Yakir-Shlez/AutoChess/Imgaes/Board/Board Inside 1.jpg

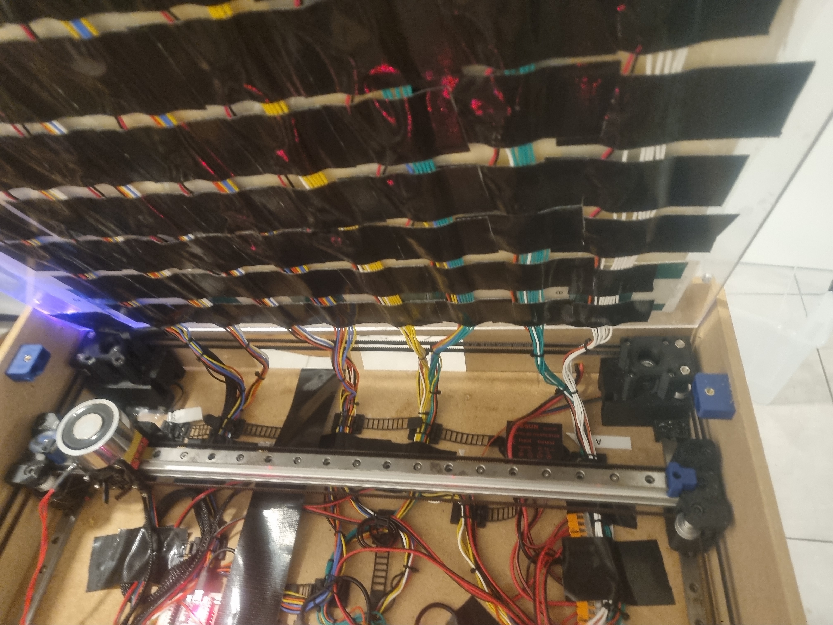
Imgaes/Board/Board Inside 1.jpg
