Yakir-Shlez/AutoChess/Imgaes/Board/Board Inside 2.jpg

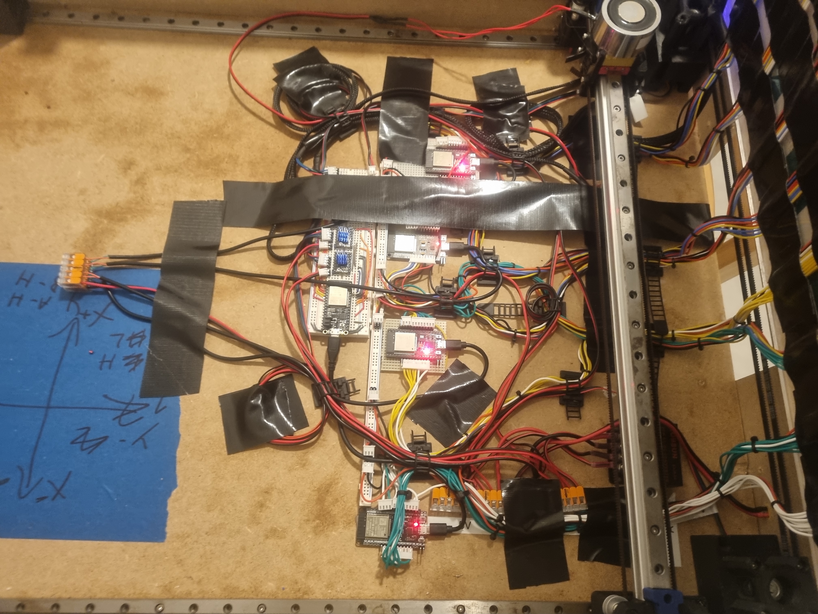
Imgaes/Board/Board Inside 2.jpg
