Yakir-Shlez/AutoChess/Imgaes/Board/Board Outside 1.jpg

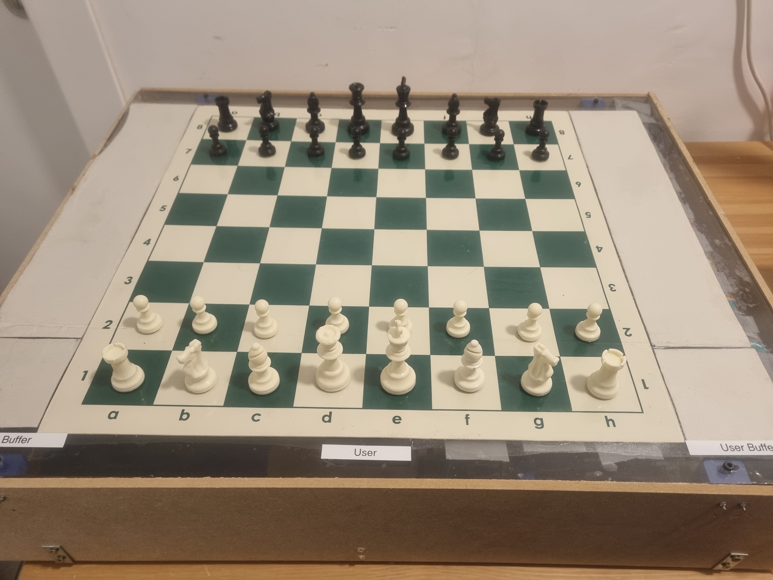
Imgaes/Board/Board Outside 1.jpg
