Yakir-Shlez/AutoChess/Imgaes/Board/Board Outside 2.jpg

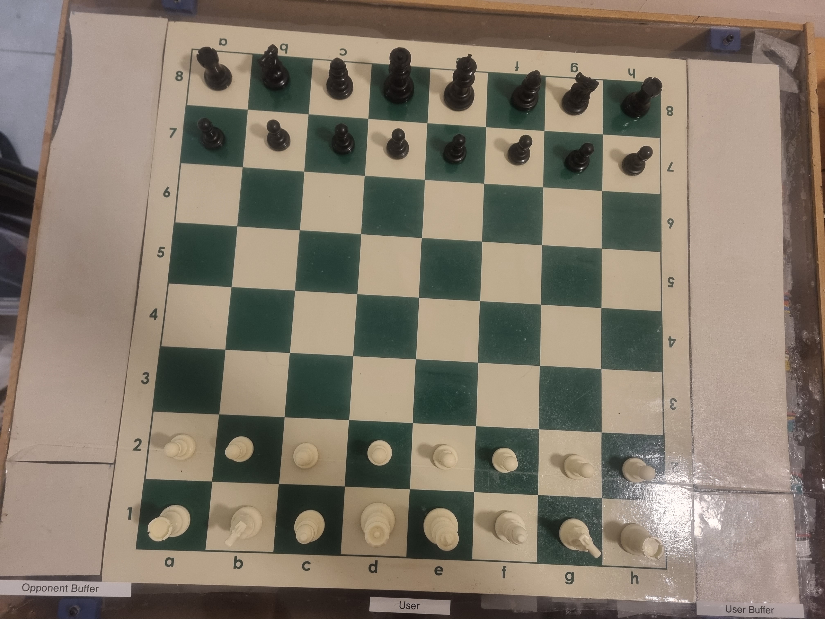
Imgaes/Board/Board Outside 2.jpg
