Yakir-Shlez/AutoChess/Imgaes/Client/Game Screen.PNG

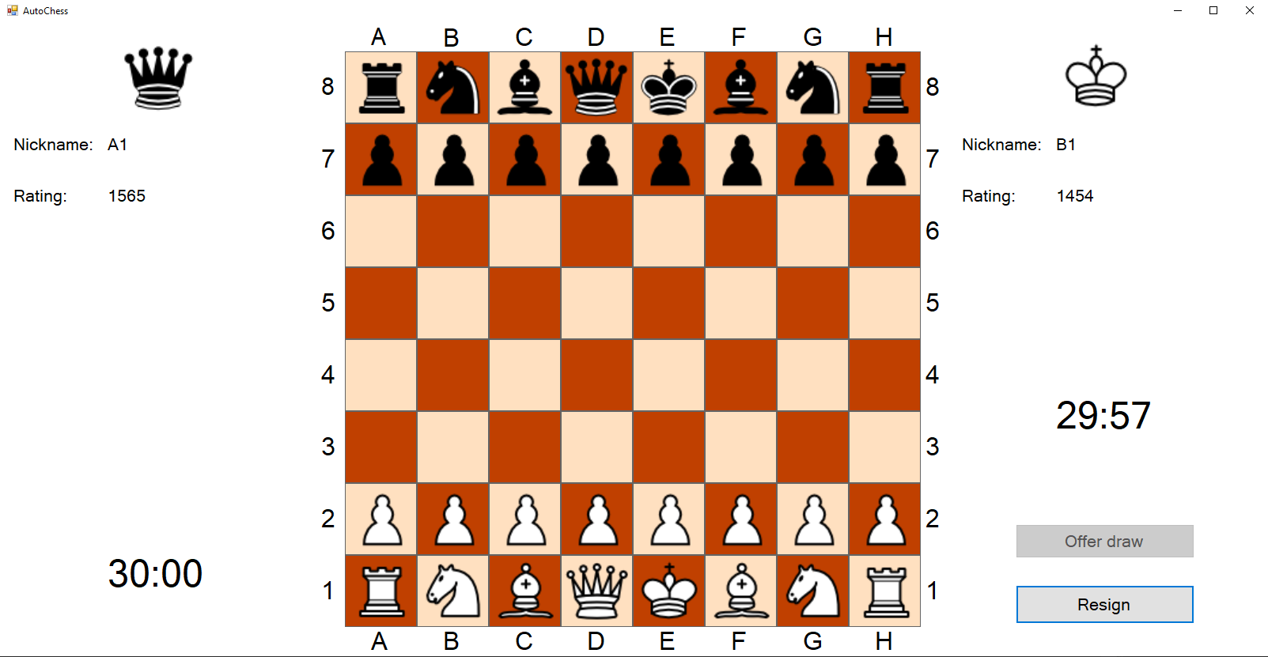
Imgaes/Client/Game Screen.PNG
