Yakir-Shlez/AutoChess/Imgaes/Client/Log In Screen.PNG

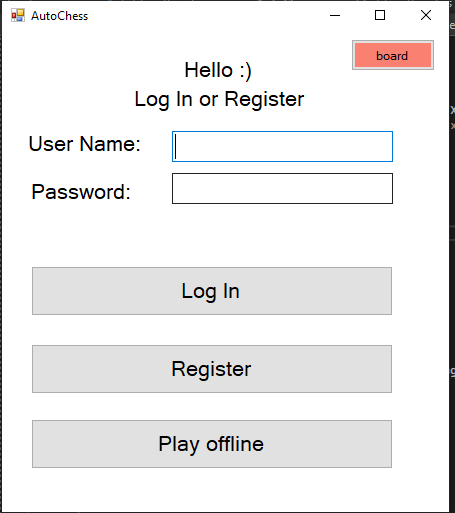
Imgaes/Client/Log In Screen.PNG
