Yakir-Shlez/AutoChess/Imgaes/Client/Main Menu Screen.PNG

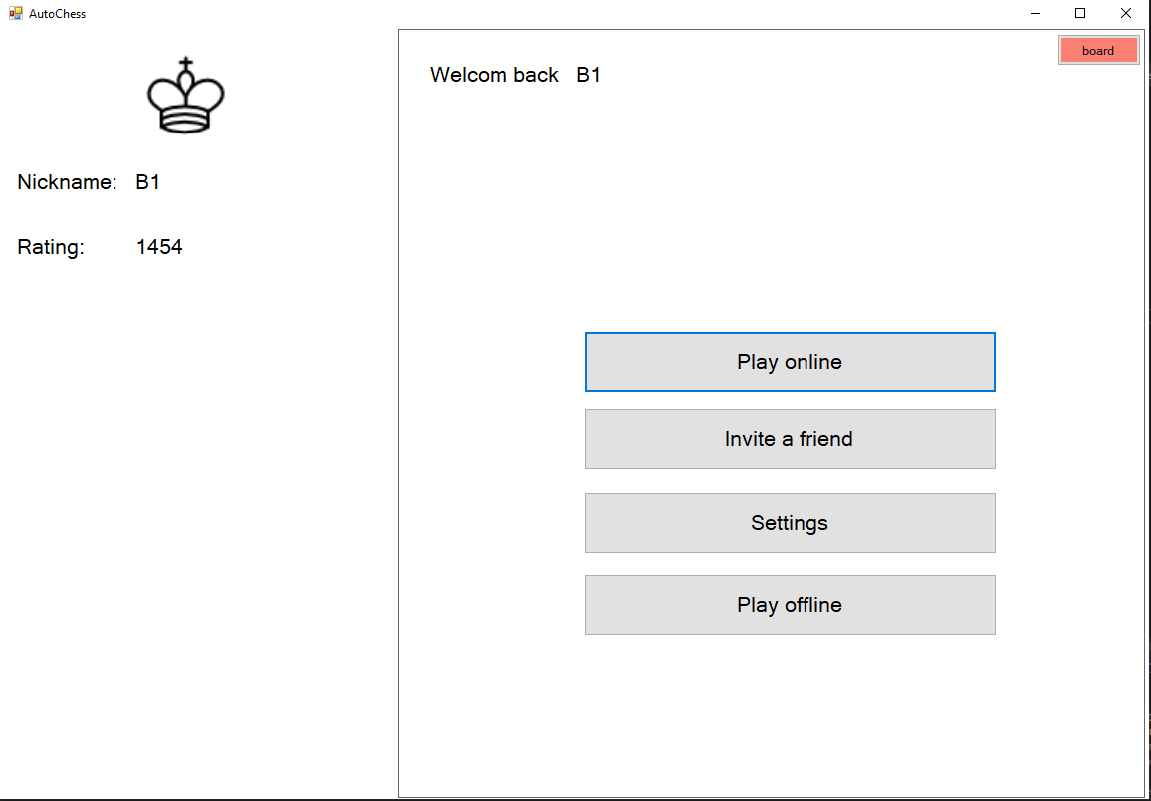
Imgaes/Client/Main Menu Screen.PNG
