Yakir-Shlez/AutoChess/Imgaes/Server/Server Off.jpg

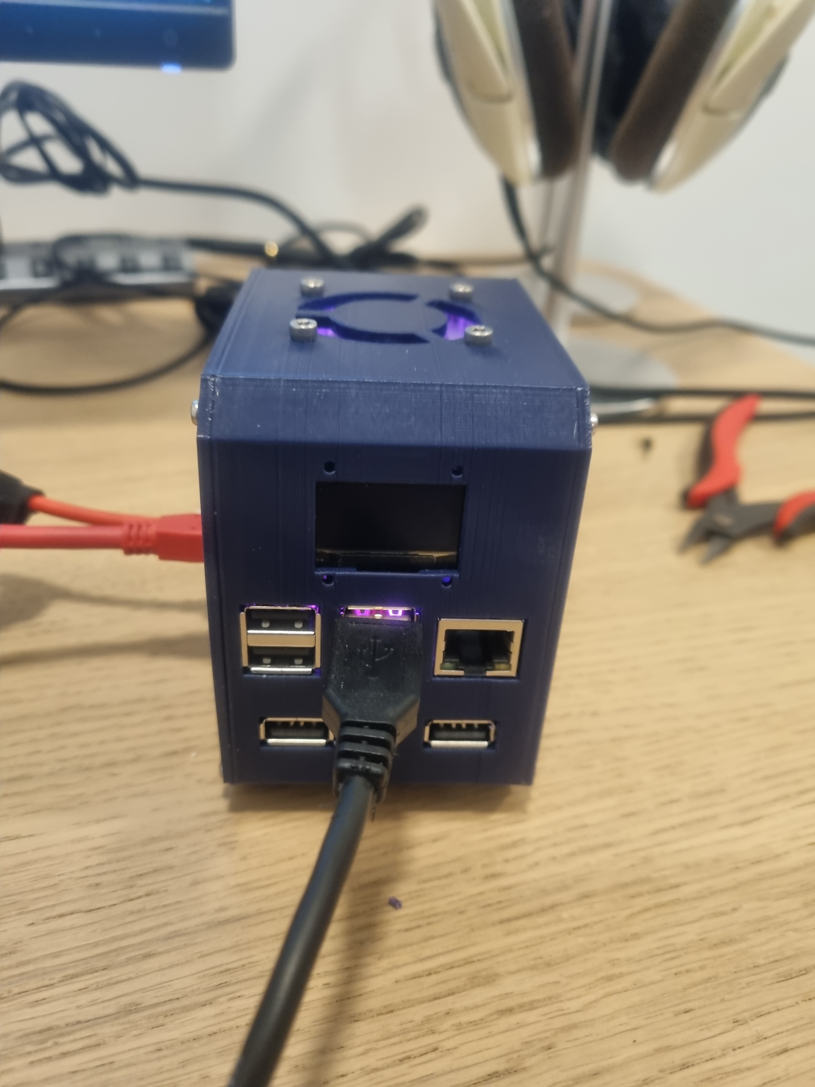
Imgaes/Server/Server Off.jpg
