Yakir-Shlez/AutoChess/Imgaes/Server/Server On.jpg

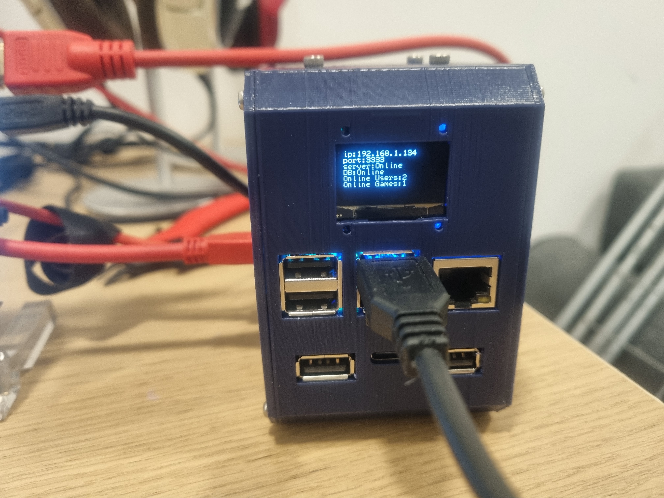
Imgaes/Server/Server On.jpg
