Yakir-Shlez/AutoChess/Imgaes/Server/Server Open.jpg

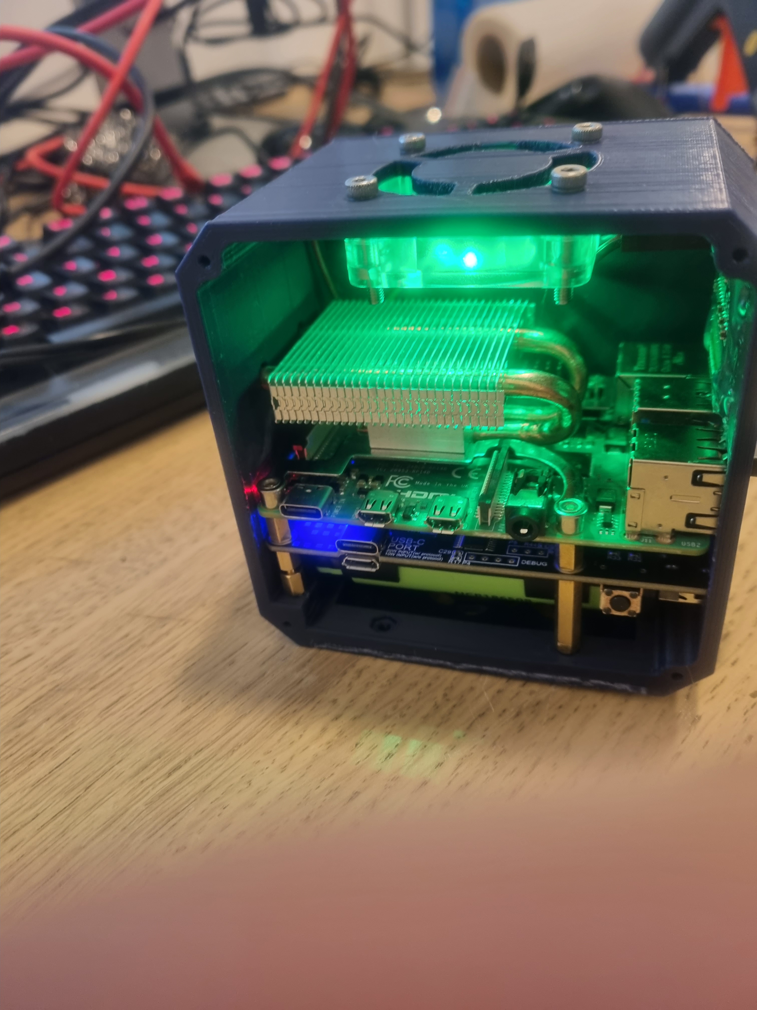
Imgaes/Server/Server Open.jpg
