Yakir-Shlez/AutoChess/Imgaes/Server/Server Screen.jpg

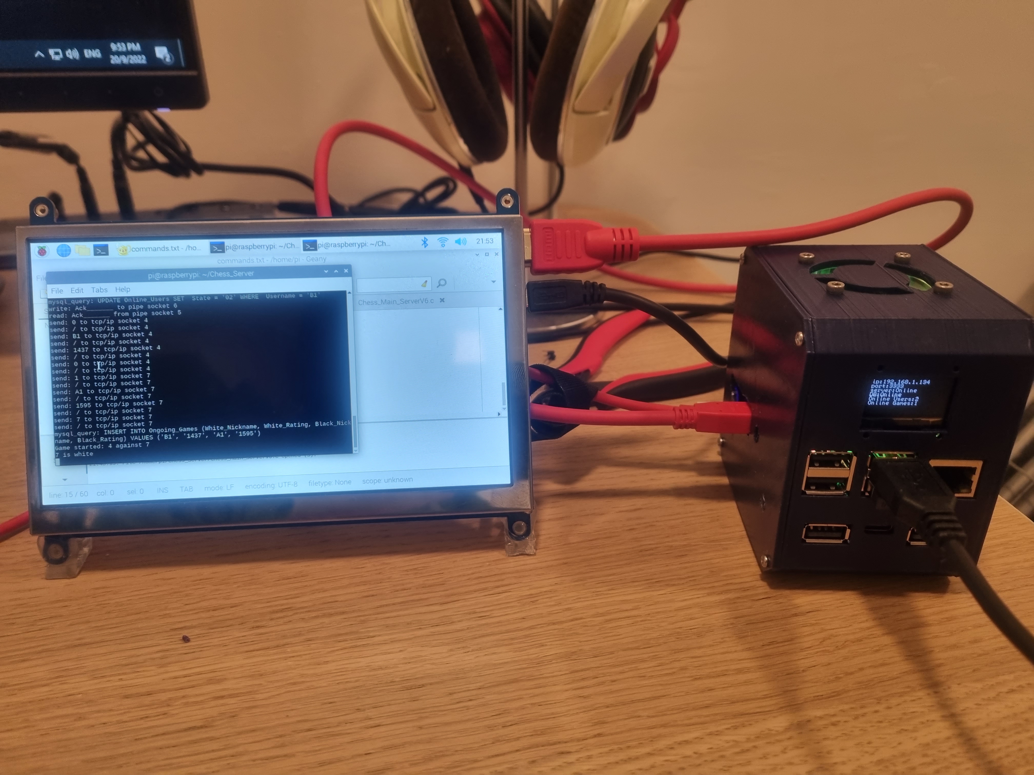
Imgaes/Server/Server Screen.jpg
