Yakir-Shlez/AutoChess/Imgaes/WIP/20210708_012601.jpg

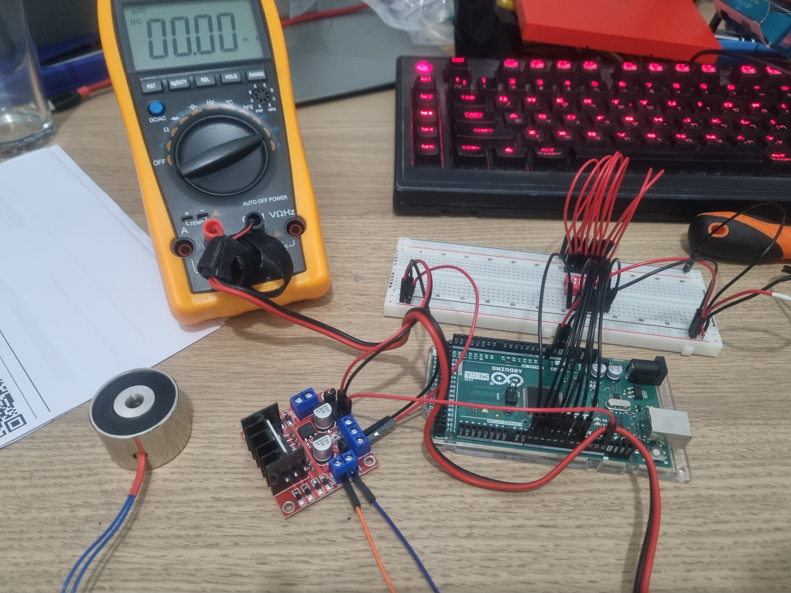
Imgaes/WIP/20210708_012601.jpg
