Yakir-Shlez/AutoChess/Imgaes/WIP/20210708_012740.jpg

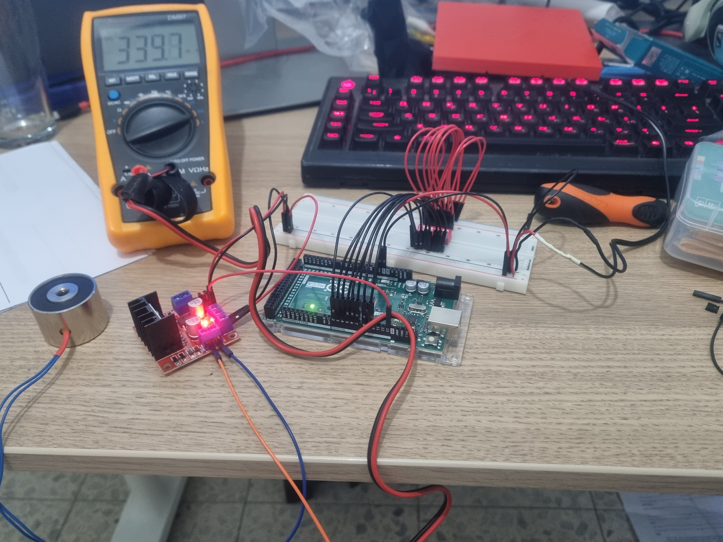
Imgaes/WIP/20210708_012740.jpg
