Yakir-Shlez/AutoChess/Imgaes/WIP/20210708_191133.jpg

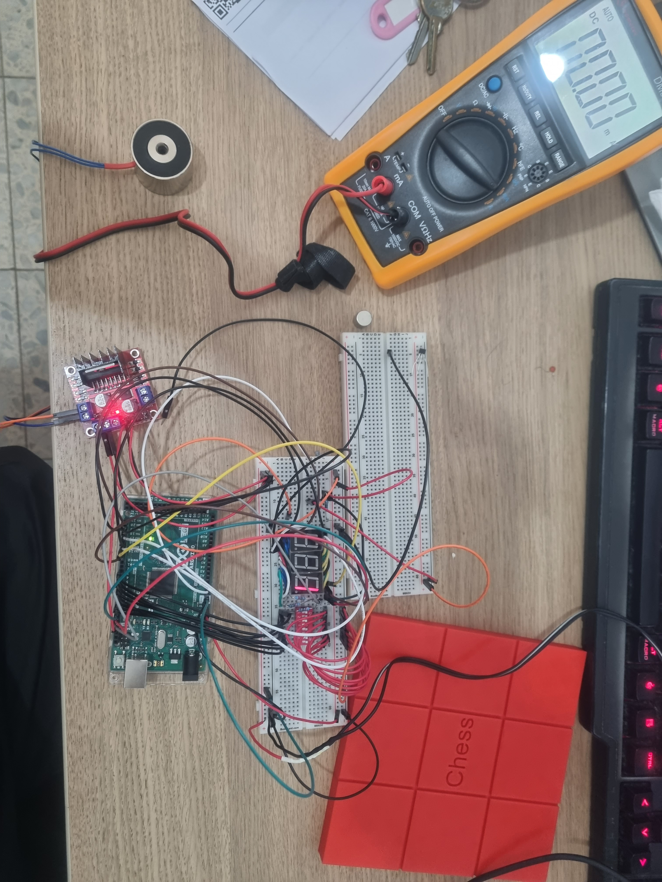
Imgaes/WIP/20210708_191133.jpg
