Yakir-Shlez/AutoChess/Imgaes/WIP/20210709_002144.jpg

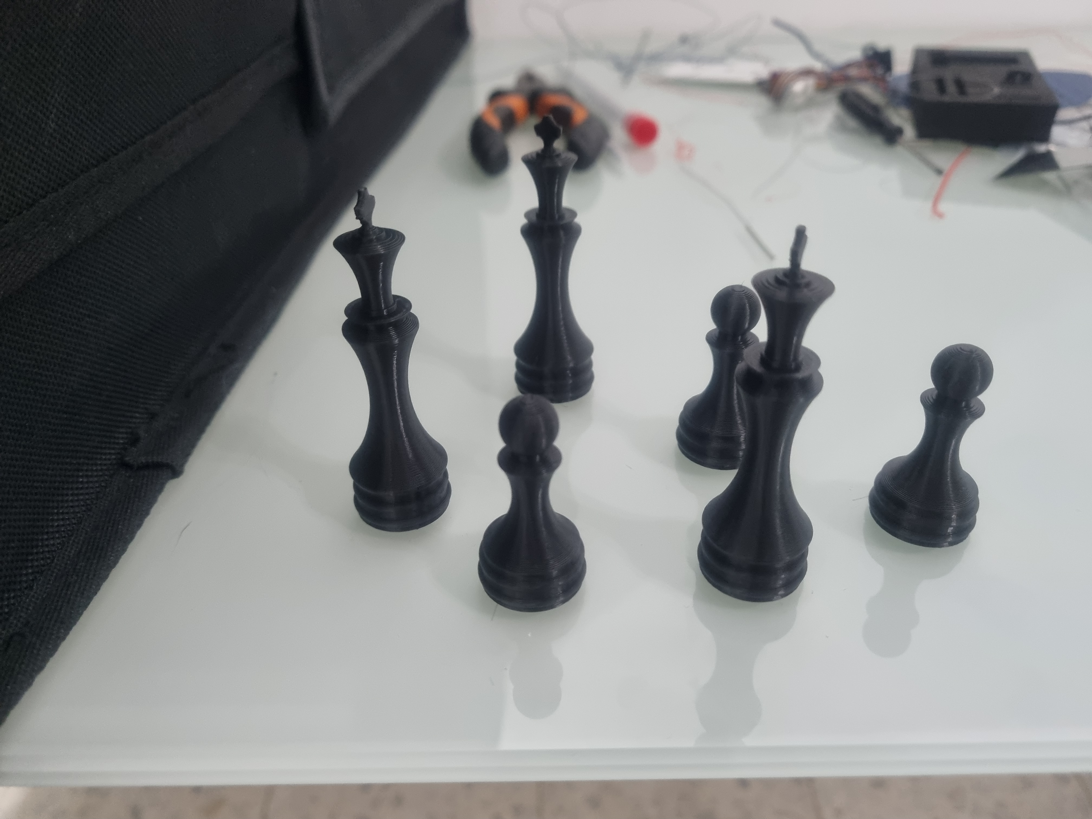
Imgaes/WIP/20210709_002144.jpg
