Yakir-Shlez/AutoChess/Imgaes/WIP/20210709_173027.jpg

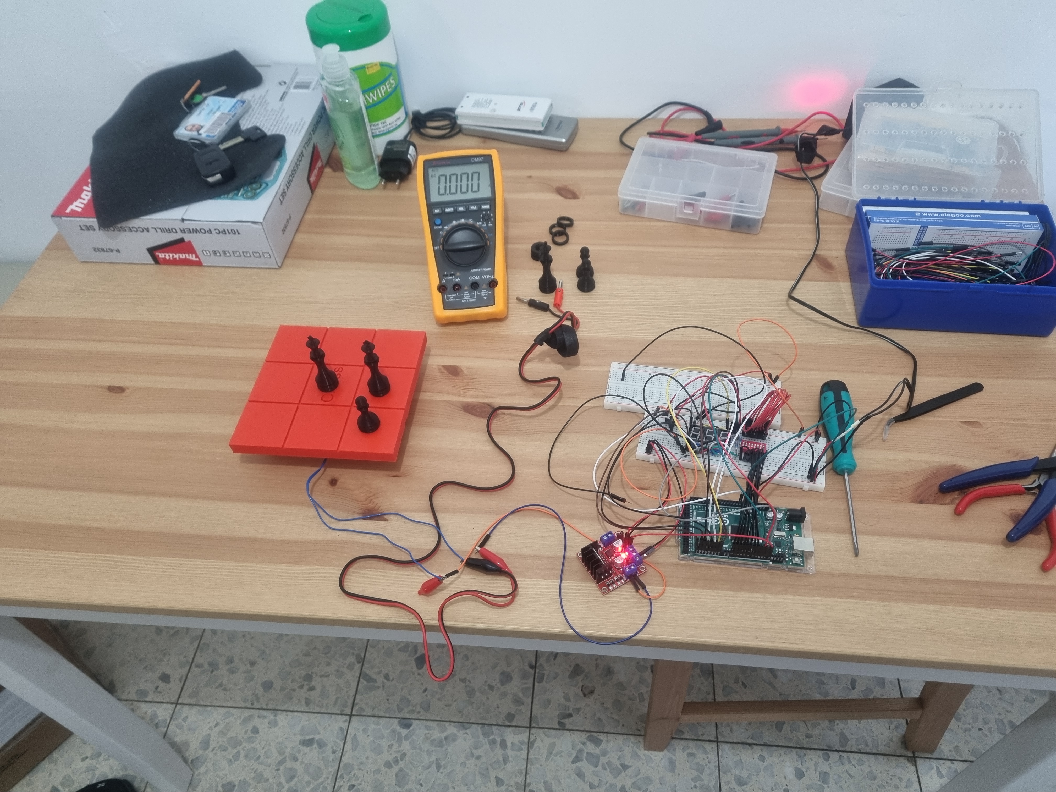
Imgaes/WIP/20210709_173027.jpg
