Yakir-Shlez/AutoChess/Imgaes/WIP/20210715_232516.jpg

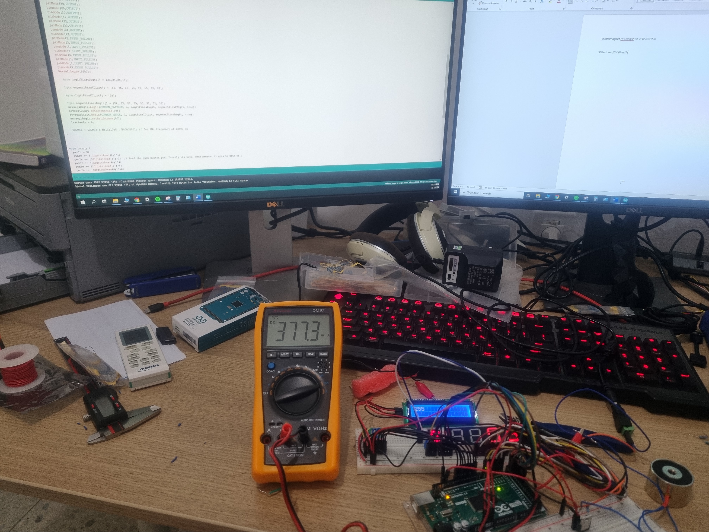
Imgaes/WIP/20210715_232516.jpg
