Yakir-Shlez/AutoChess/Imgaes/WIP/20210715_232529.jpg

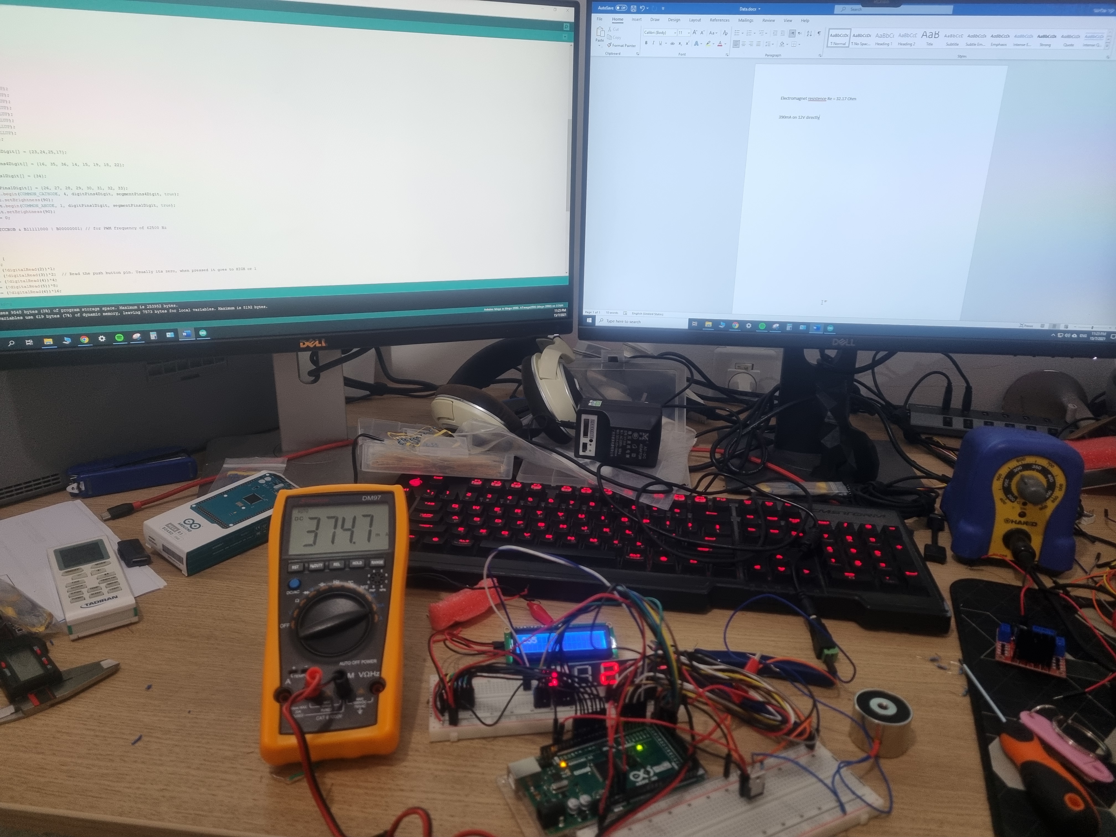
Imgaes/WIP/20210715_232529.jpg
