Yakir-Shlez/AutoChess/Imgaes/WIP/20210715_232534.jpg

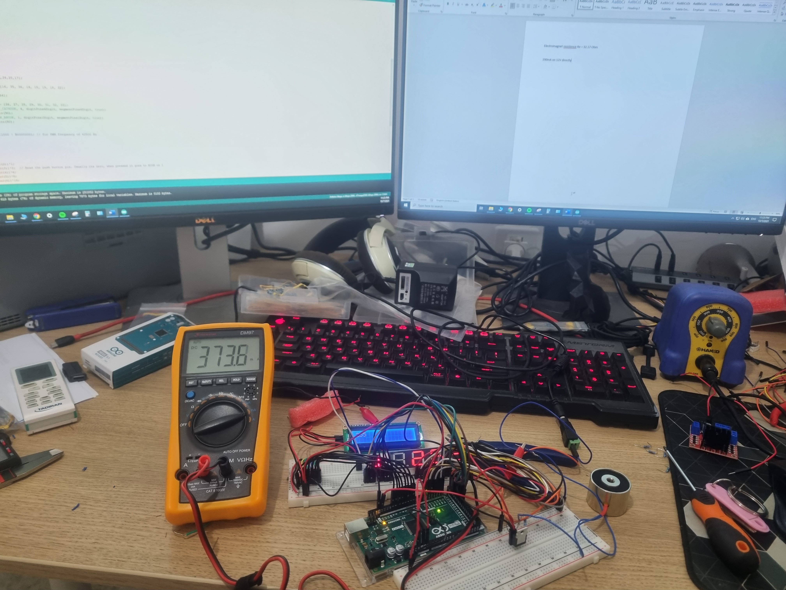
Imgaes/WIP/20210715_232534.jpg
