Yakir-Shlez/AutoChess/Imgaes/WIP/20210715_232541.jpg

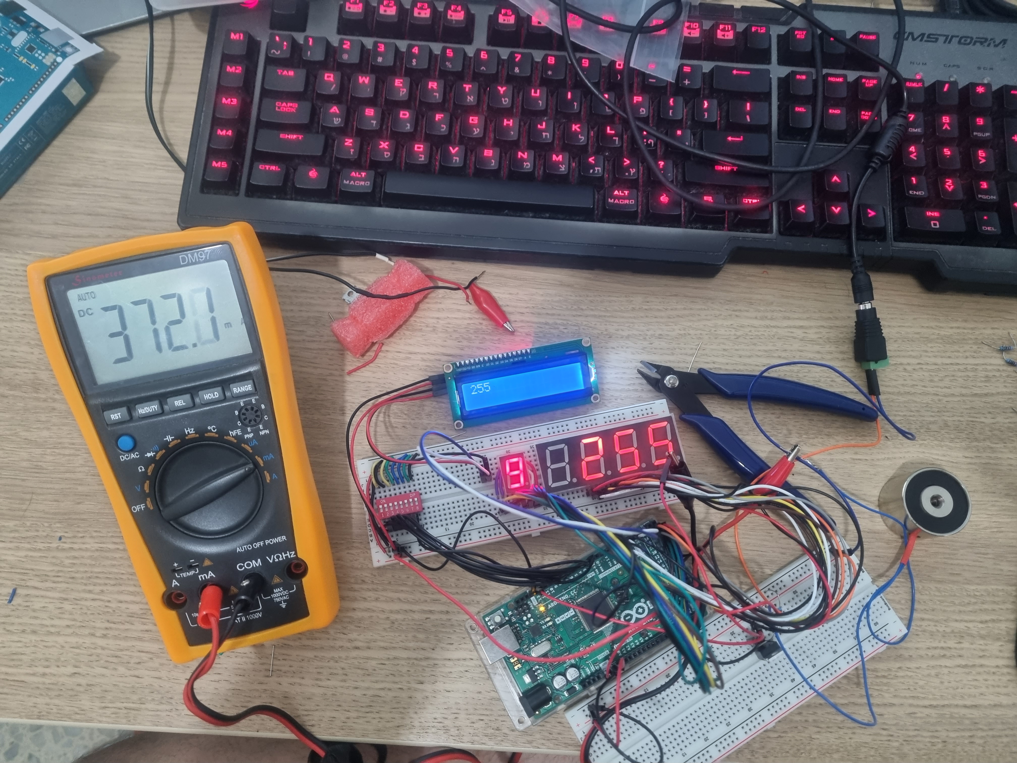
Imgaes/WIP/20210715_232541.jpg
