Yakir-Shlez/AutoChess/Imgaes/WIP/20210722_215017.jpg

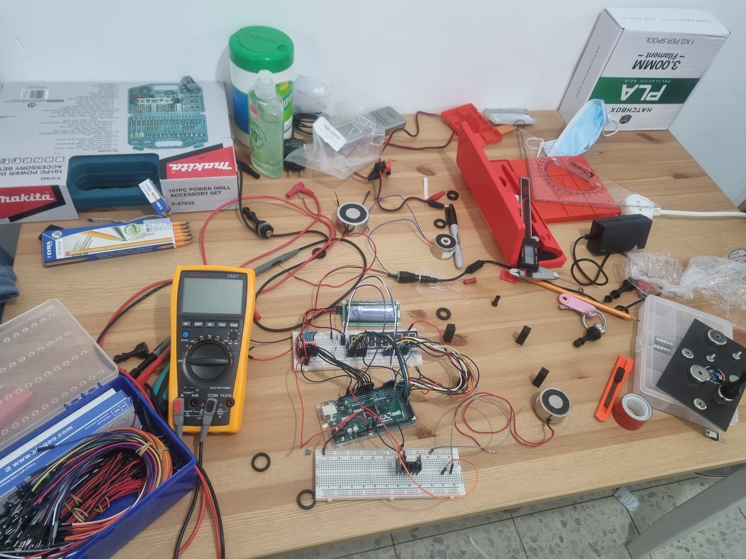
Imgaes/WIP/20210722_215017.jpg
