Yakir-Shlez/AutoChess/Imgaes/WIP/20210724_002252.jpg

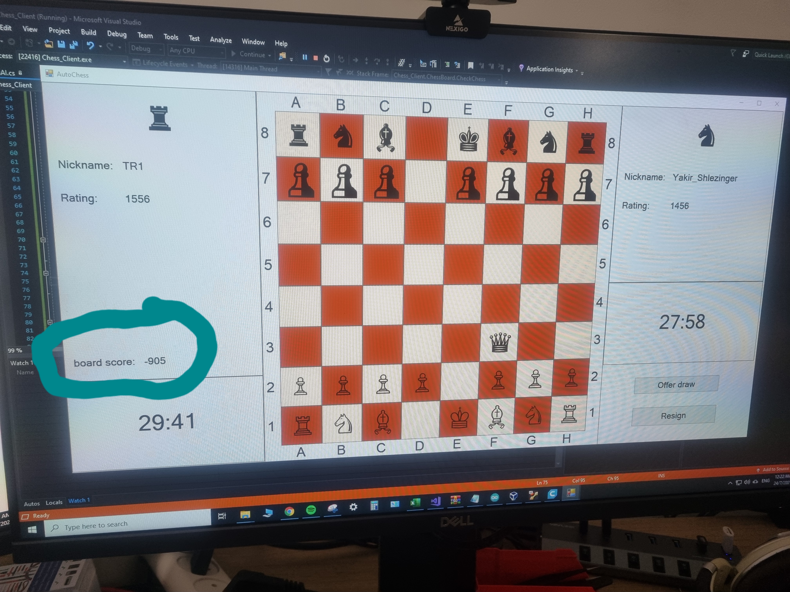
Imgaes/WIP/20210724_002252.jpg
