Yakir-Shlez/AutoChess/Imgaes/WIP/20210724_130340.jpg

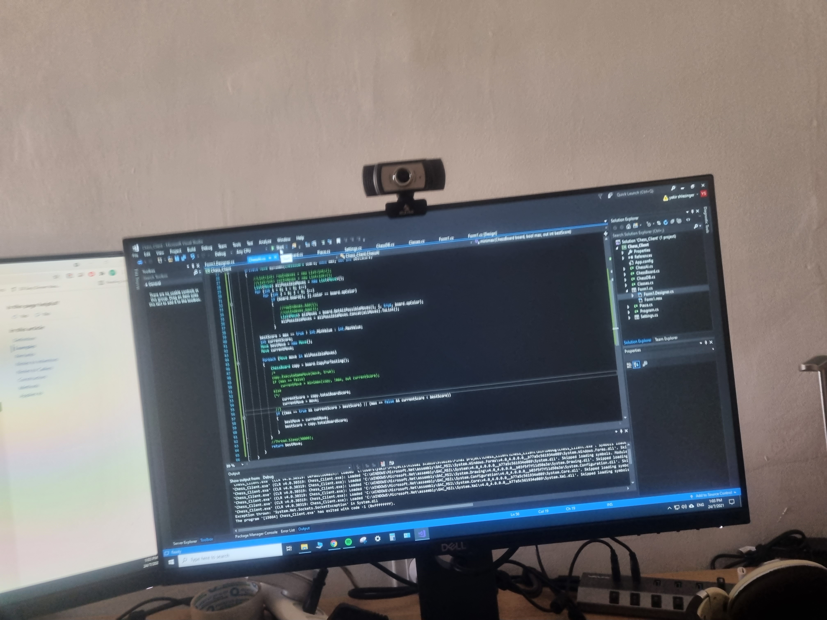
Imgaes/WIP/20210724_130340.jpg
