Yakir-Shlez/AutoChess/Imgaes/WIP/20210727_054952.jpg

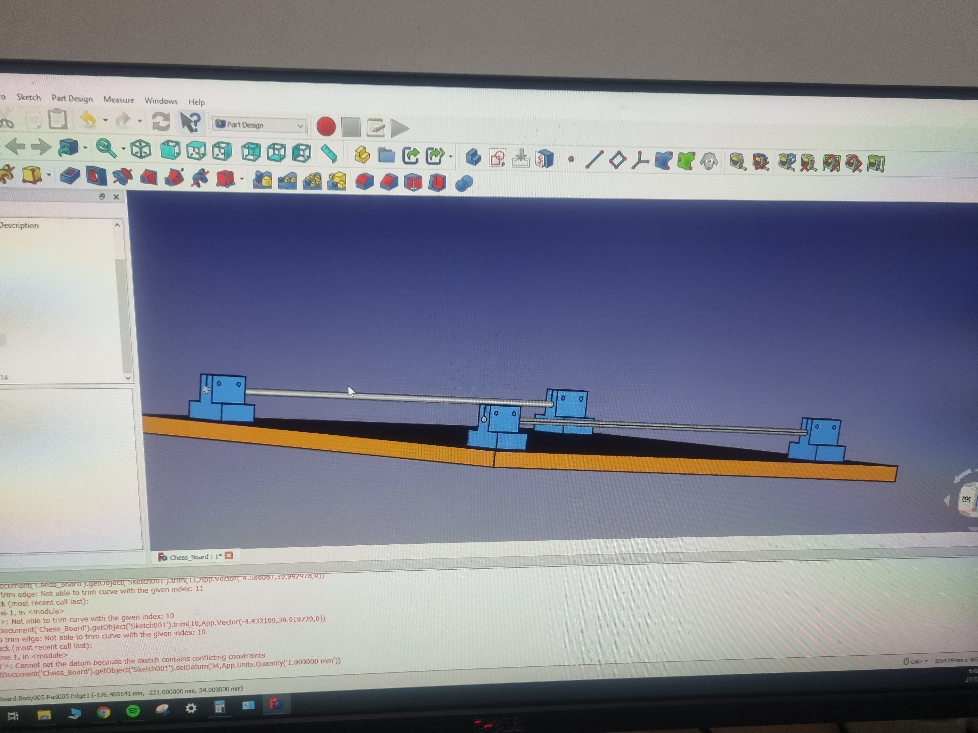
Imgaes/WIP/20210727_054952.jpg
