Yakir-Shlez/AutoChess/Imgaes/WIP/20210731_223613.jpg

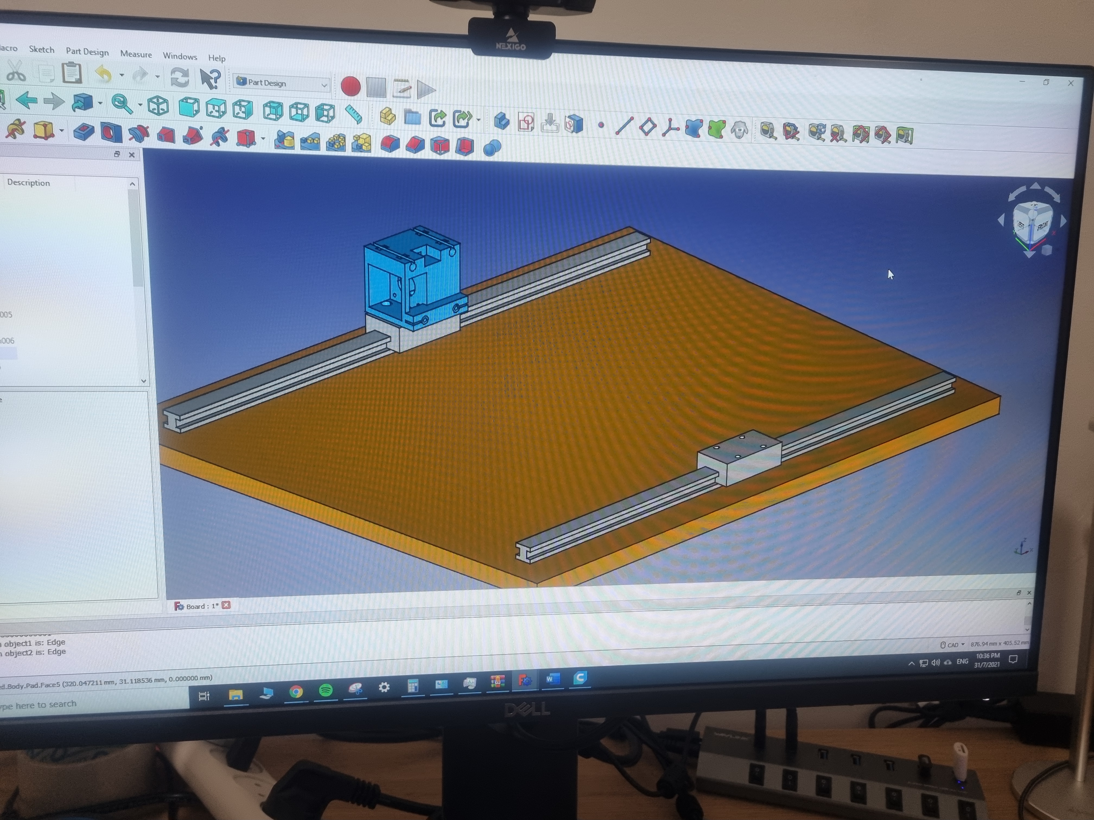
Imgaes/WIP/20210731_223613.jpg
