Yakir-Shlez/AutoChess/Imgaes/WIP/20210731_234115.jpg

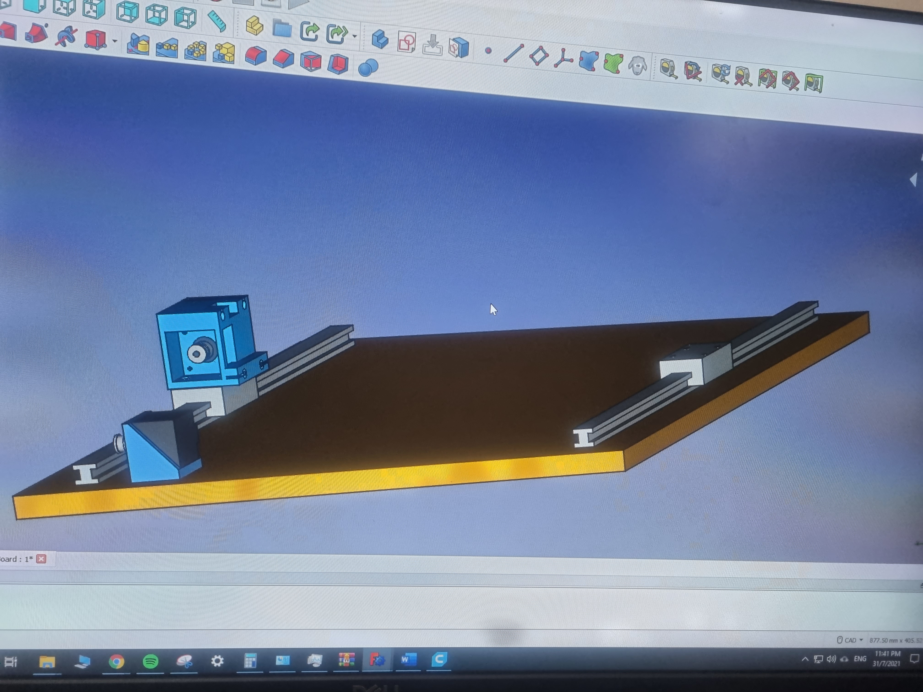
Imgaes/WIP/20210731_234115.jpg
