Yakir-Shlez/AutoChess/Imgaes/WIP/20210801_025701.jpg

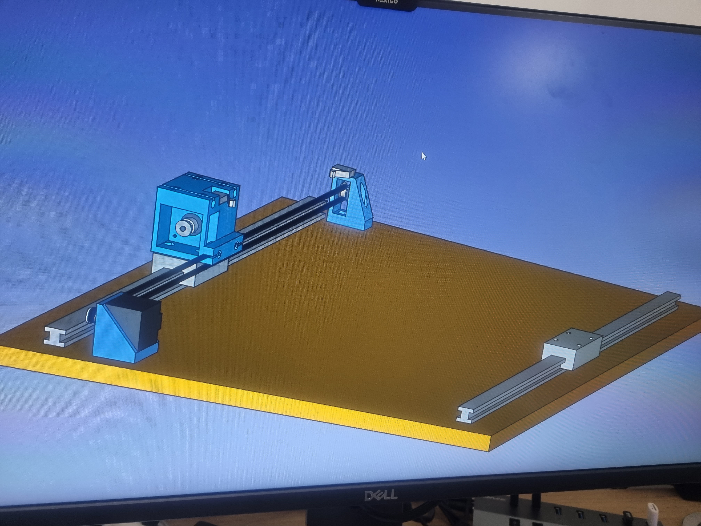
Imgaes/WIP/20210801_025701.jpg
