Yakir-Shlez/AutoChess/Imgaes/WIP/20210801_025935.jpg

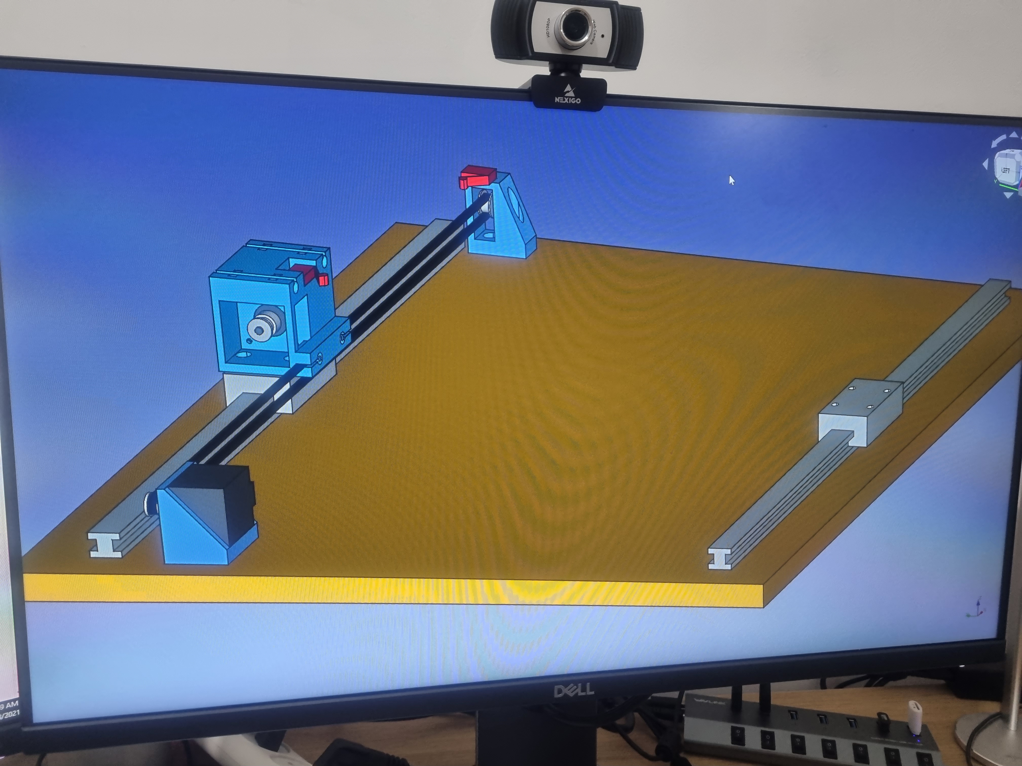
Imgaes/WIP/20210801_025935.jpg
