Yakir-Shlez/AutoChess/Imgaes/WIP/20210801_035938.jpg

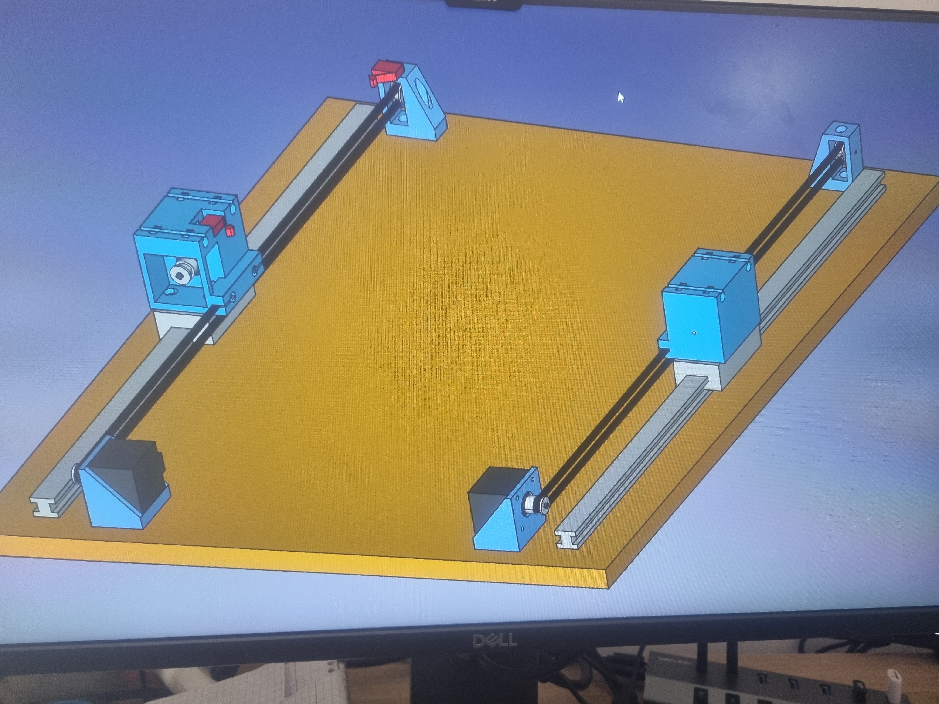
Imgaes/WIP/20210801_035938.jpg
