Yakir-Shlez/AutoChess/Imgaes/WIP/20210801_040600.jpg

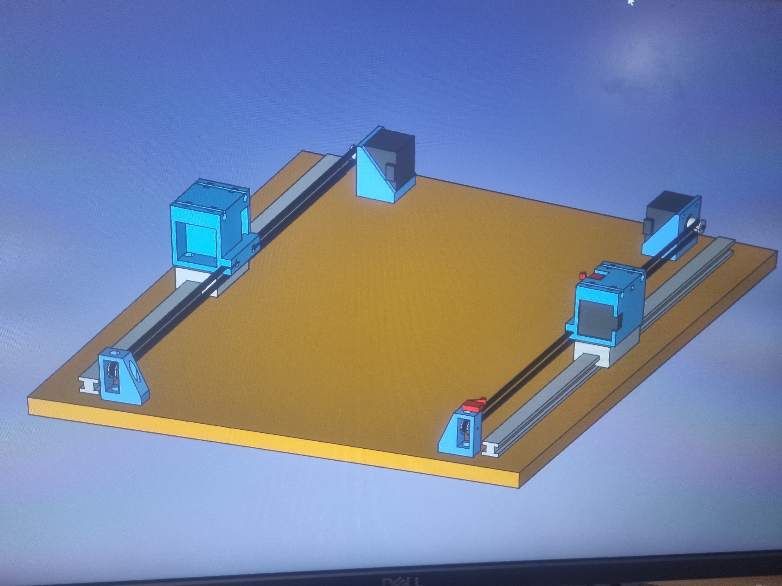
Imgaes/WIP/20210801_040600.jpg
