Yakir-Shlez/AutoChess/Imgaes/WIP/20210801_040831.jpg

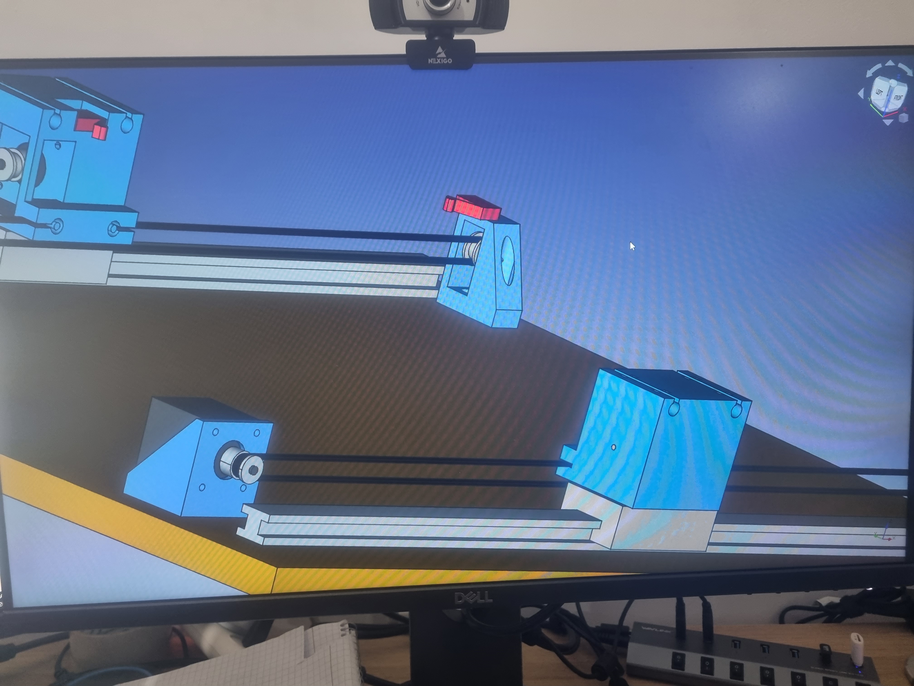
Imgaes/WIP/20210801_040831.jpg
