Yakir-Shlez/AutoChess/Imgaes/WIP/20210801_052911.jpg

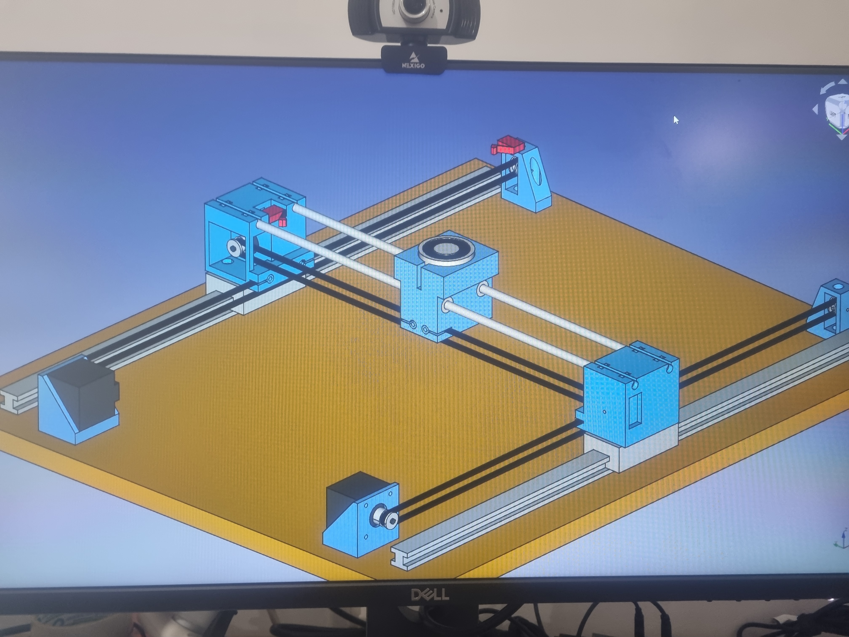
Imgaes/WIP/20210801_052911.jpg
