Yakir-Shlez/AutoChess/Imgaes/WIP/20210801_053046.jpg

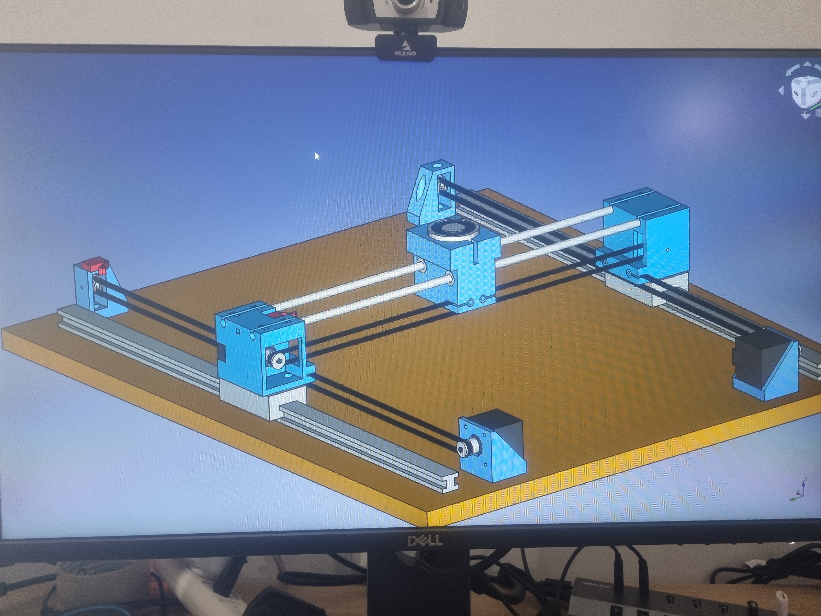
Imgaes/WIP/20210801_053046.jpg
