Yakir-Shlez/AutoChess/Imgaes/WIP/20210801_055255.jpg

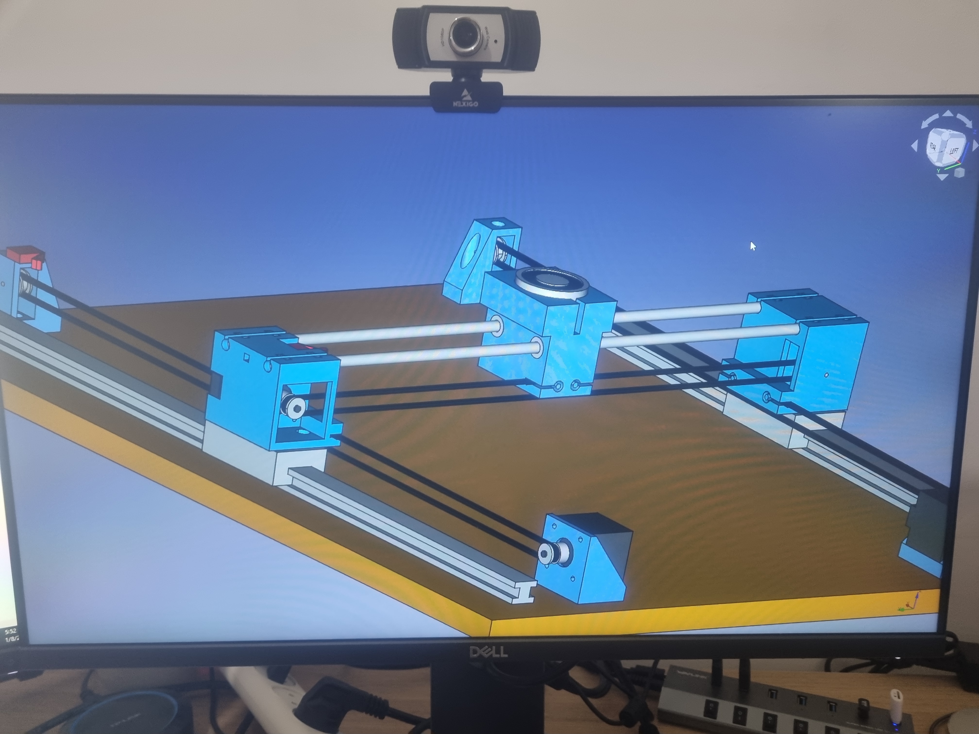
Imgaes/WIP/20210801_055255.jpg
