Yakir-Shlez/AutoChess/Imgaes/WIP/20210801_055333.jpg

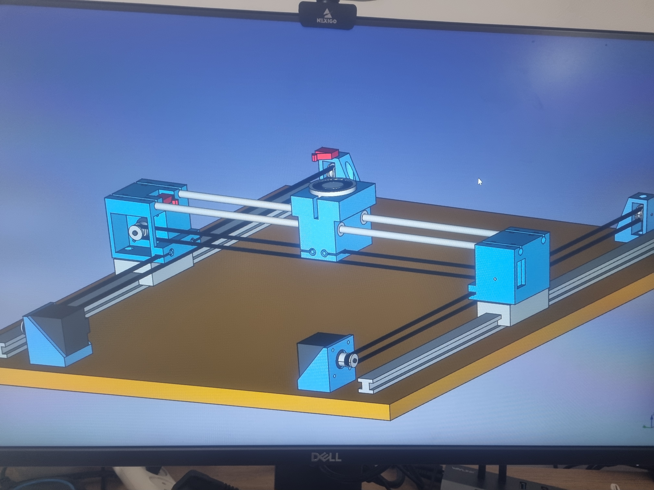
Imgaes/WIP/20210801_055333.jpg
