Yakir-Shlez/AutoChess/Imgaes/WIP/20210816_194603.jpg

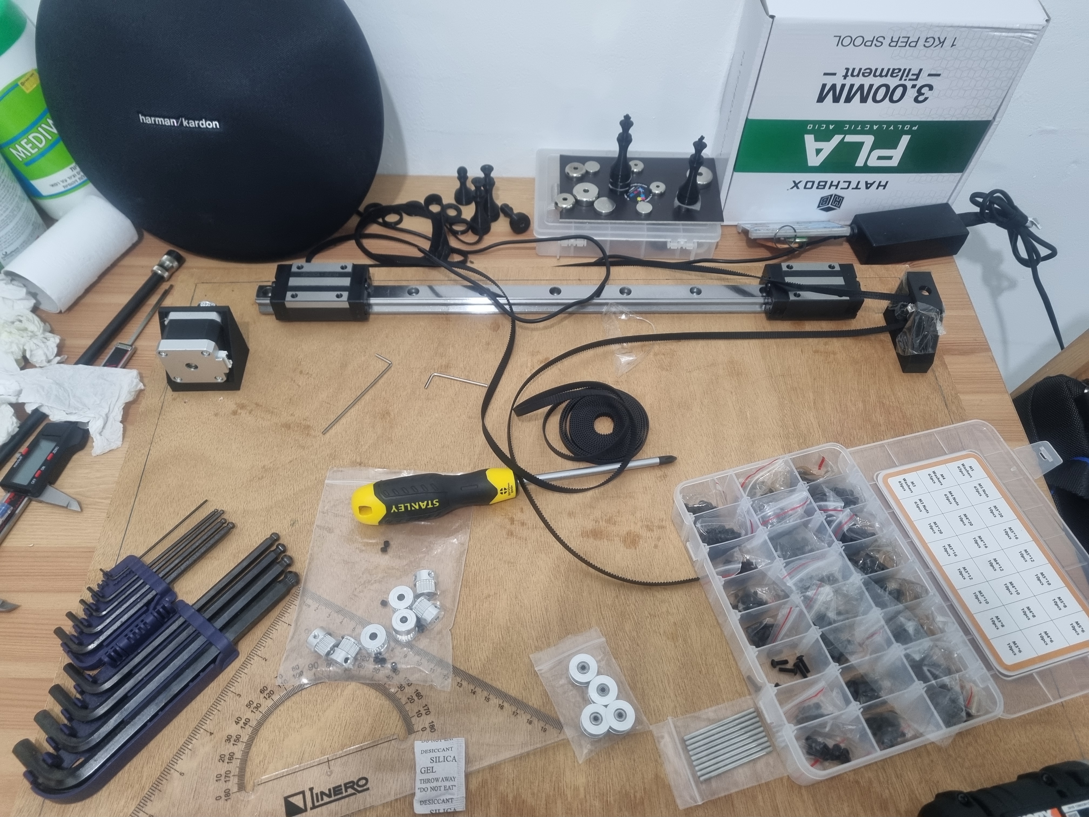
Imgaes/WIP/20210816_194603.jpg
