Yakir-Shlez/AutoChess/Imgaes/WIP/20210816_194617.jpg

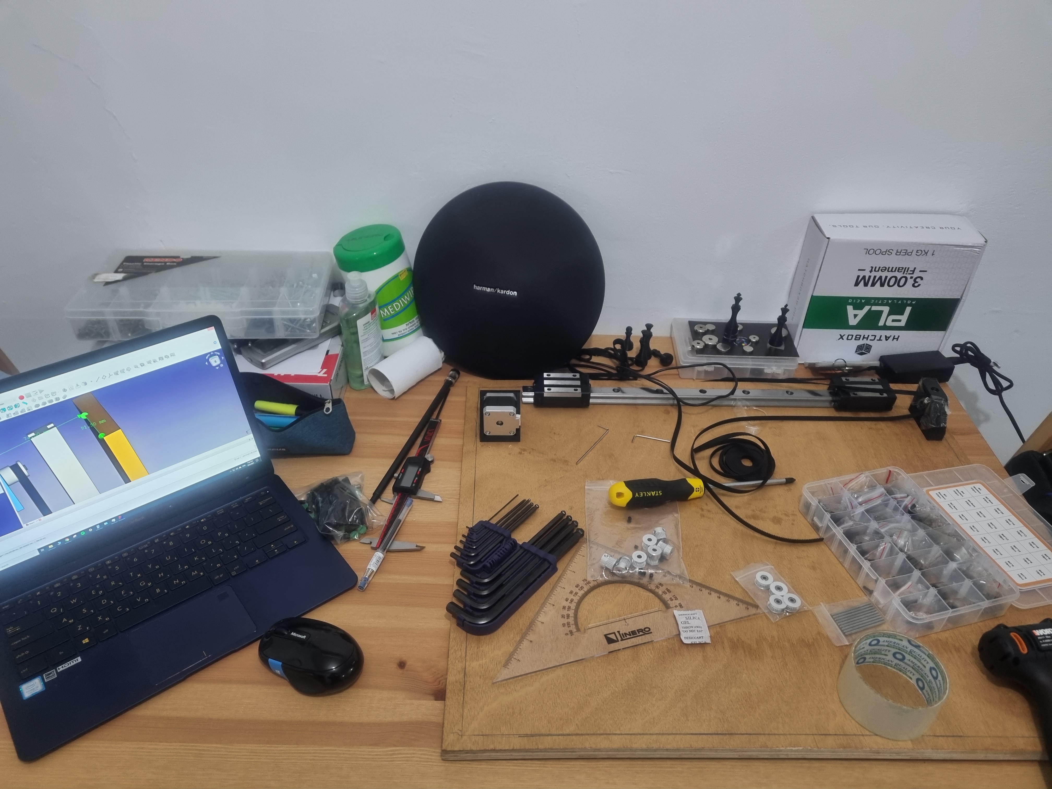
Imgaes/WIP/20210816_194617.jpg
