Yakir-Shlez/AutoChess/Imgaes/WIP/20211106_215429.jpg

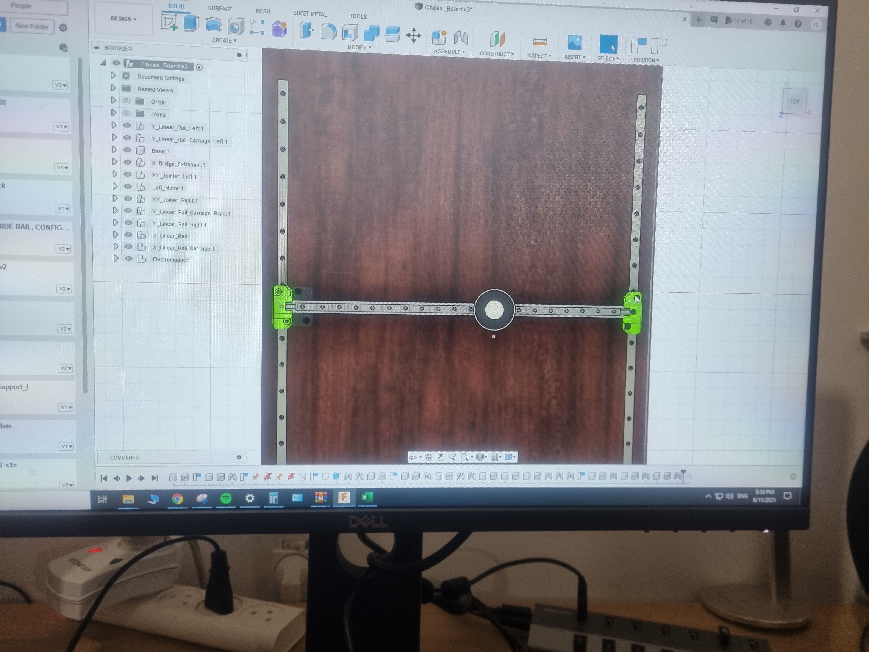
Imgaes/WIP/20211106_215429.jpg
