Yakir-Shlez/AutoChess/Imgaes/WIP/20211125_202150.jpg

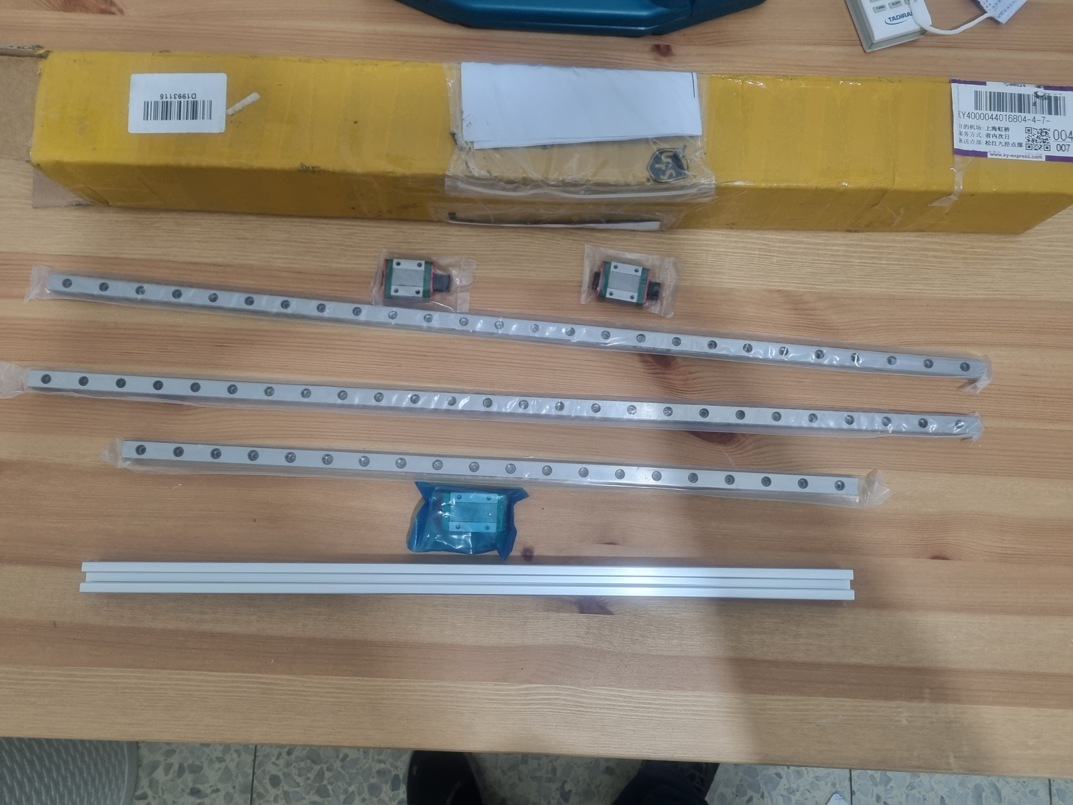
Imgaes/WIP/20211125_202150.jpg
