Yakir-Shlez/AutoChess/Imgaes/WIP/20220408_162342.jpg

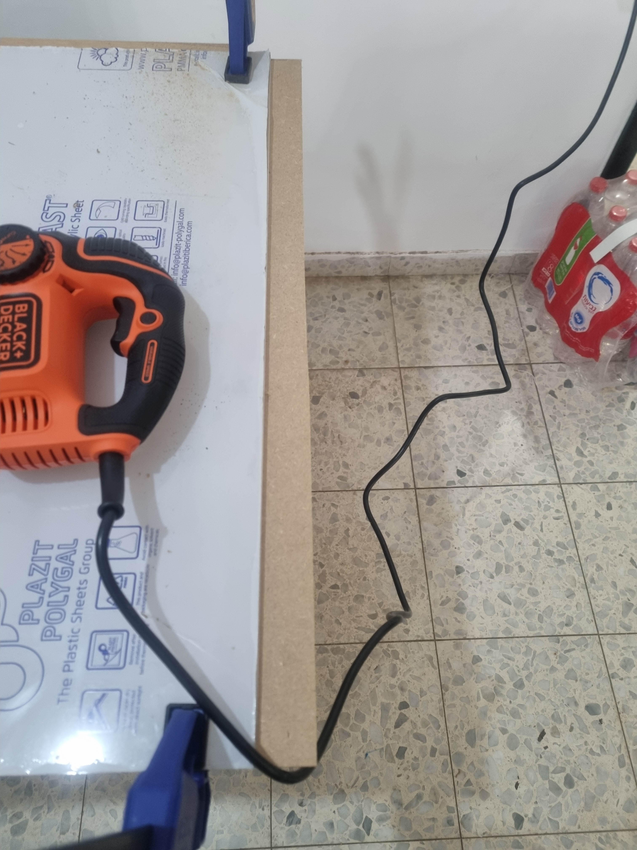
Imgaes/WIP/20220408_162342.jpg
