Yakir-Shlez/AutoChess/Imgaes/WIP/20220408_162356.jpg

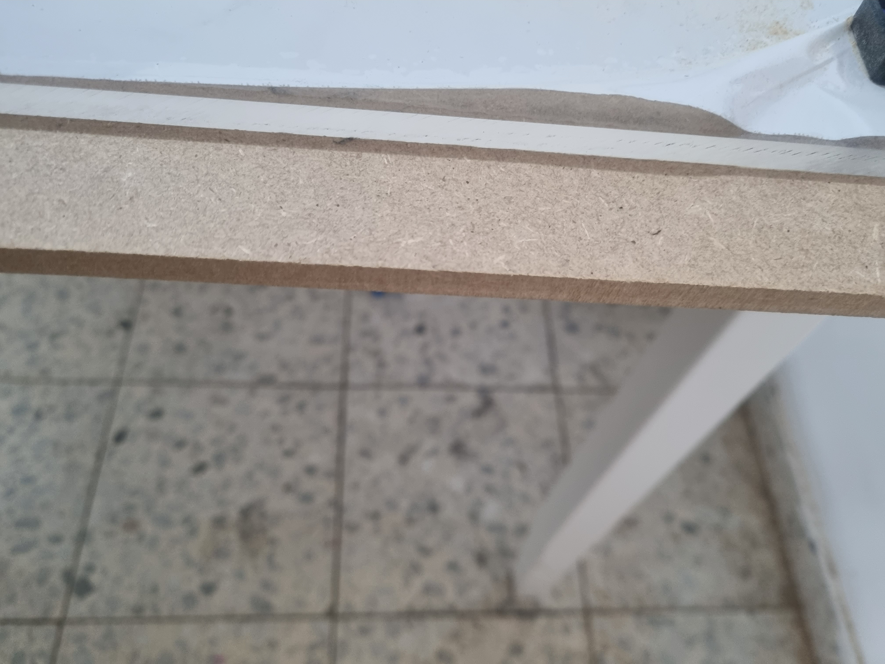
Imgaes/WIP/20220408_162356.jpg
