Yakir-Shlez/AutoChess/Imgaes/WIP/20220408_162821.jpg

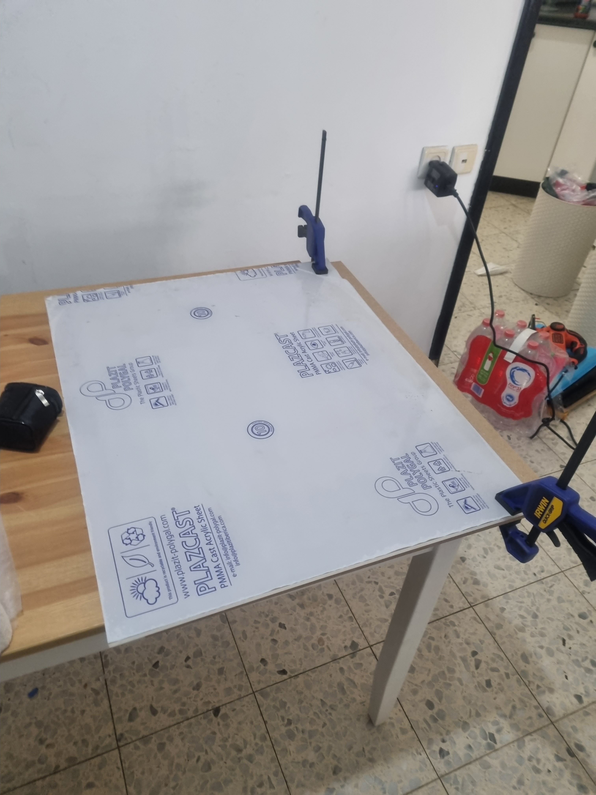
Imgaes/WIP/20220408_162821.jpg
