Yakir-Shlez/AutoChess/Imgaes/WIP/20220408_163001.jpg

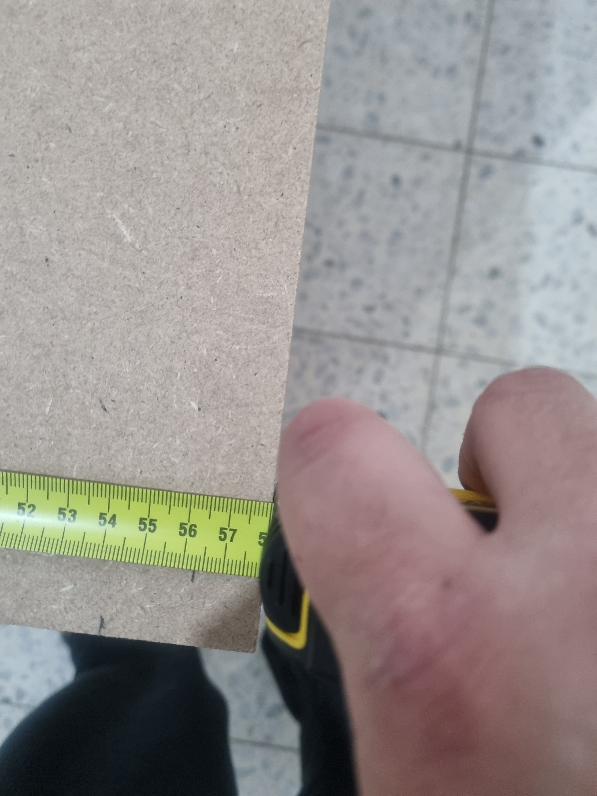
Imgaes/WIP/20220408_163001.jpg
