Yakir-Shlez/AutoChess/Imgaes/WIP/20220408_163010.jpg

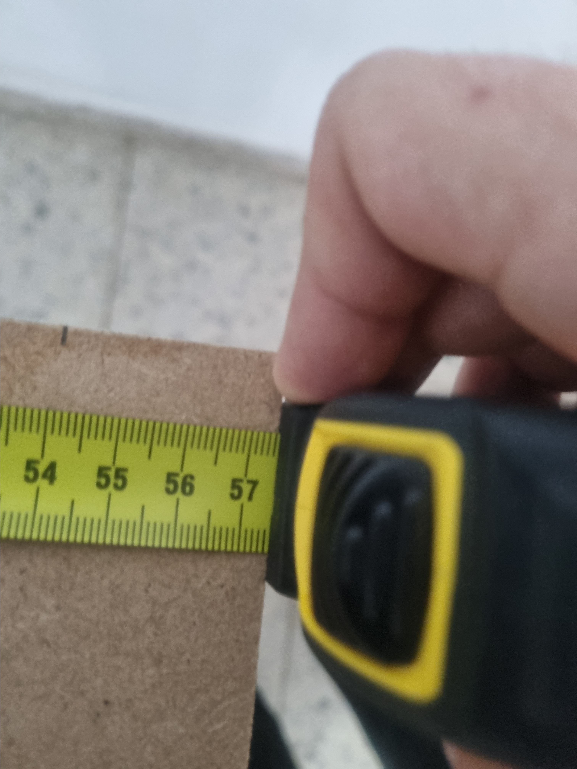
Imgaes/WIP/20220408_163010.jpg
