Yakir-Shlez/AutoChess/Imgaes/WIP/20220408_164139.jpg

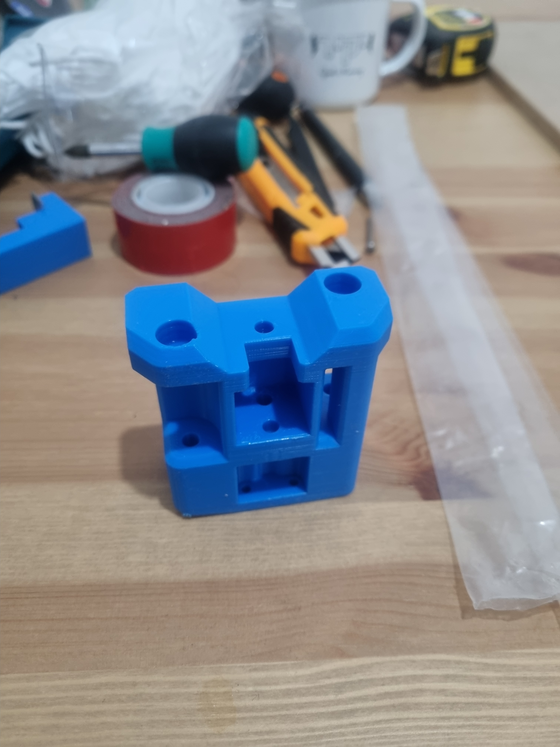
Imgaes/WIP/20220408_164139.jpg
