Yakir-Shlez/AutoChess/Imgaes/WIP/20220408_164146.jpg

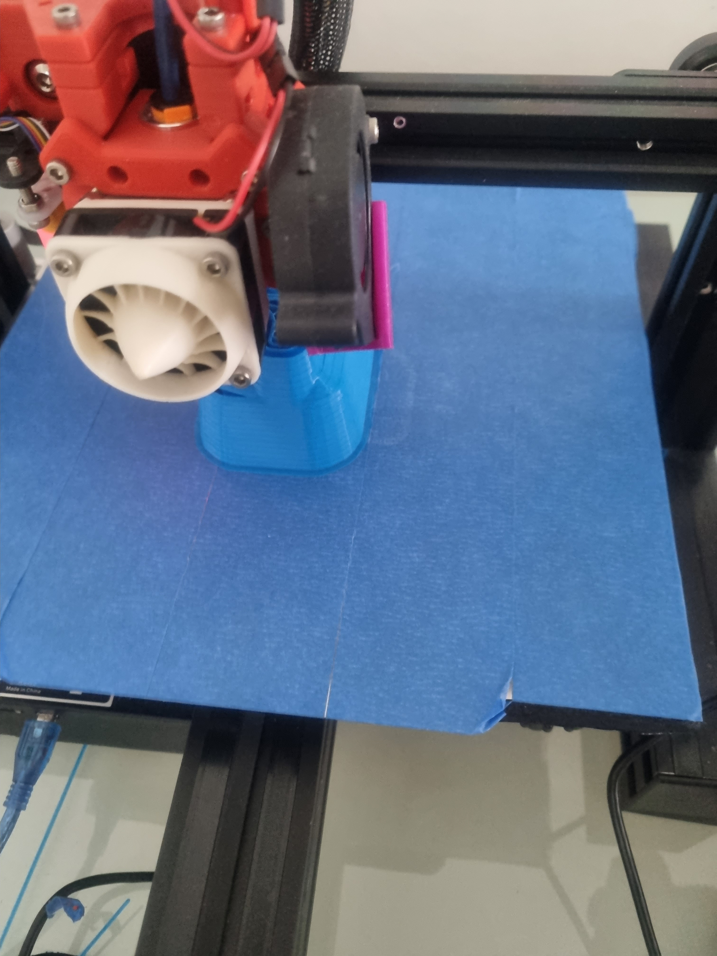
Imgaes/WIP/20220408_164146.jpg
