Yakir-Shlez/AutoChess/Imgaes/WIP/20220408_164151.jpg

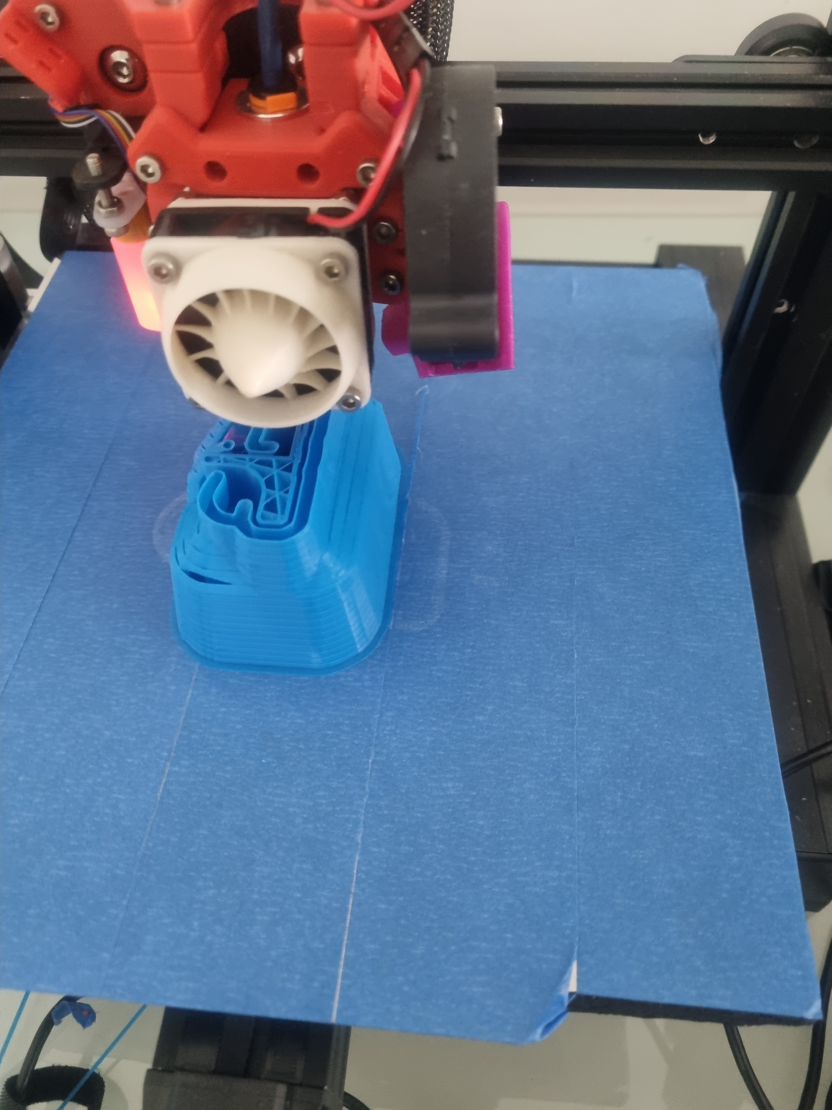
Imgaes/WIP/20220408_164151.jpg
