Yakir-Shlez/AutoChess/Imgaes/WIP/20220408_164943.jpg

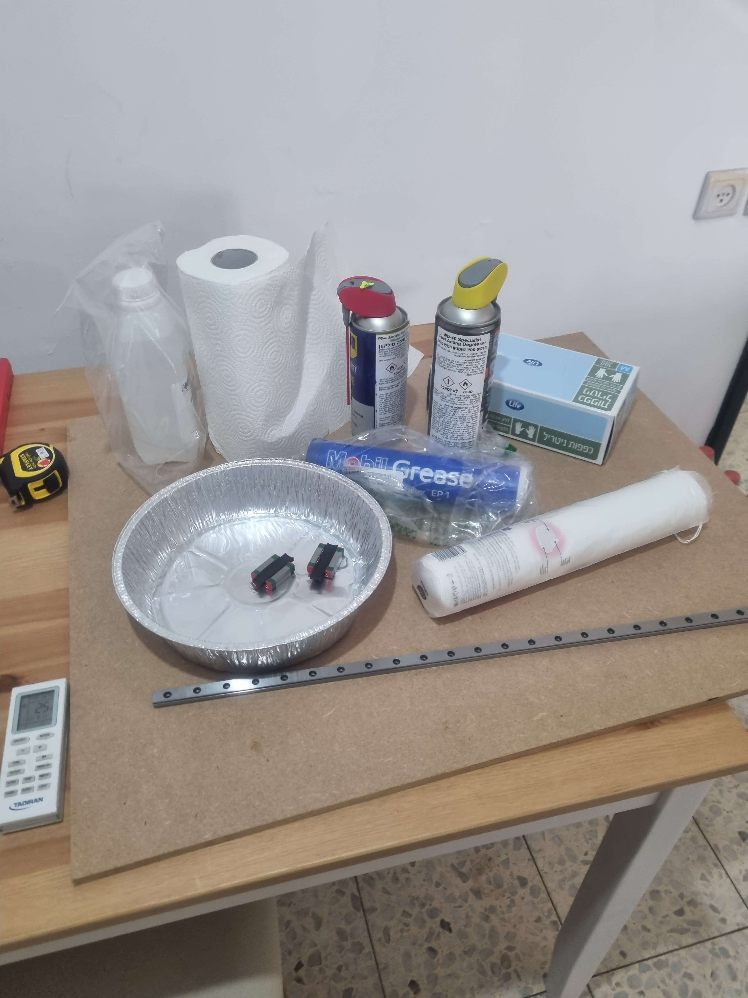
Imgaes/WIP/20220408_164943.jpg
