Yakir-Shlez/AutoChess/Imgaes/WIP/20220408_165838.jpg

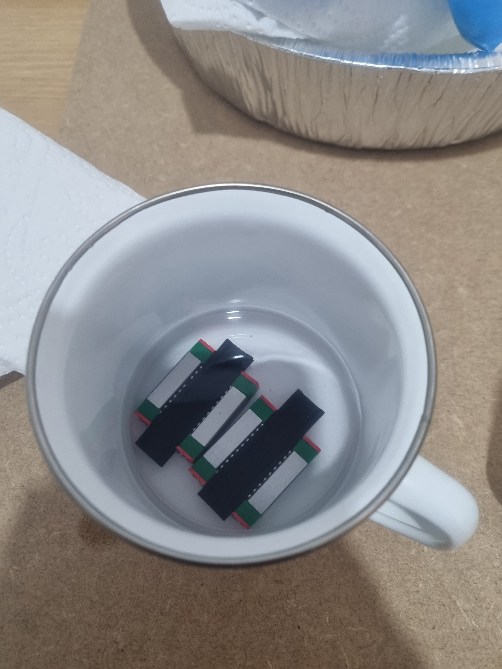
Imgaes/WIP/20220408_165838.jpg
