Yakir-Shlez/AutoChess/Imgaes/WIP/20220408_194540.jpg

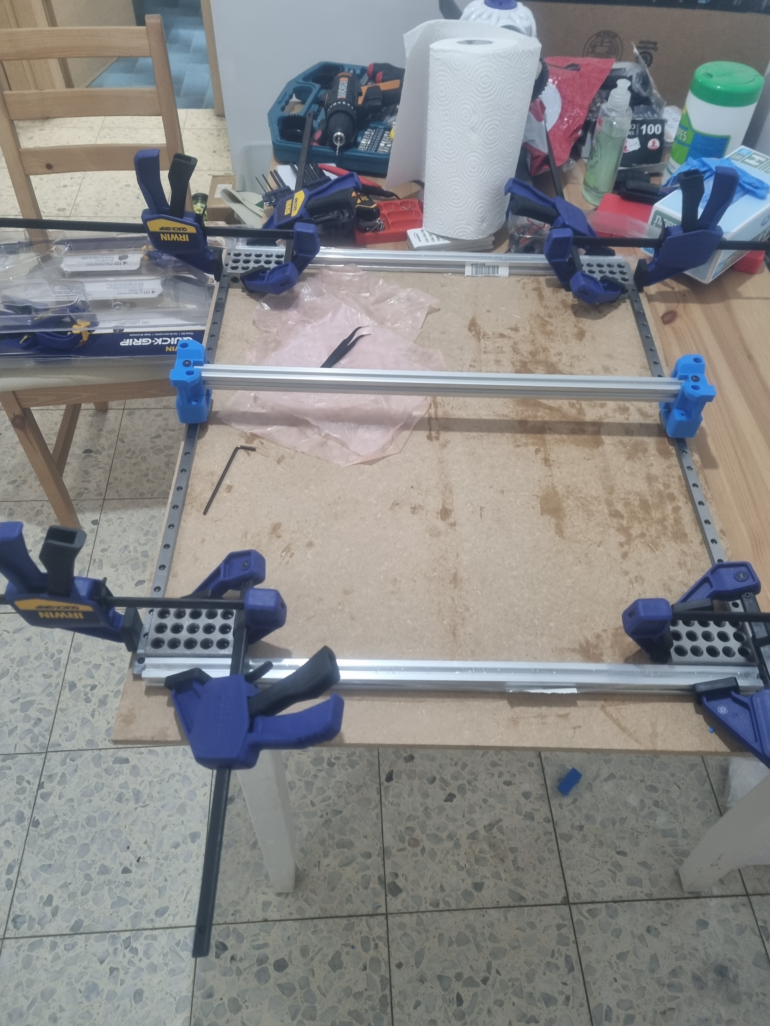
Imgaes/WIP/20220408_194540.jpg
