Yakir-Shlez/AutoChess/Imgaes/WIP/20220412_021302.jpg

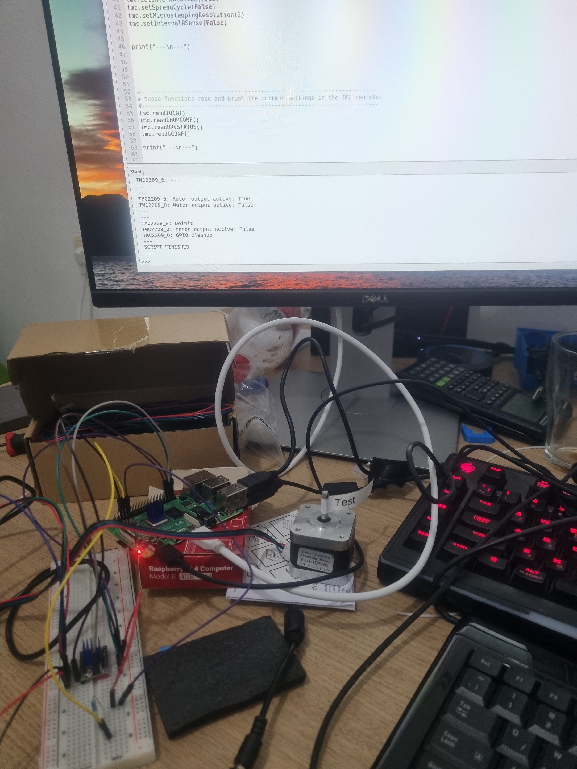
Imgaes/WIP/20220412_021302.jpg
