Yakir-Shlez/AutoChess/Imgaes/WIP/20220412_033123.jpg

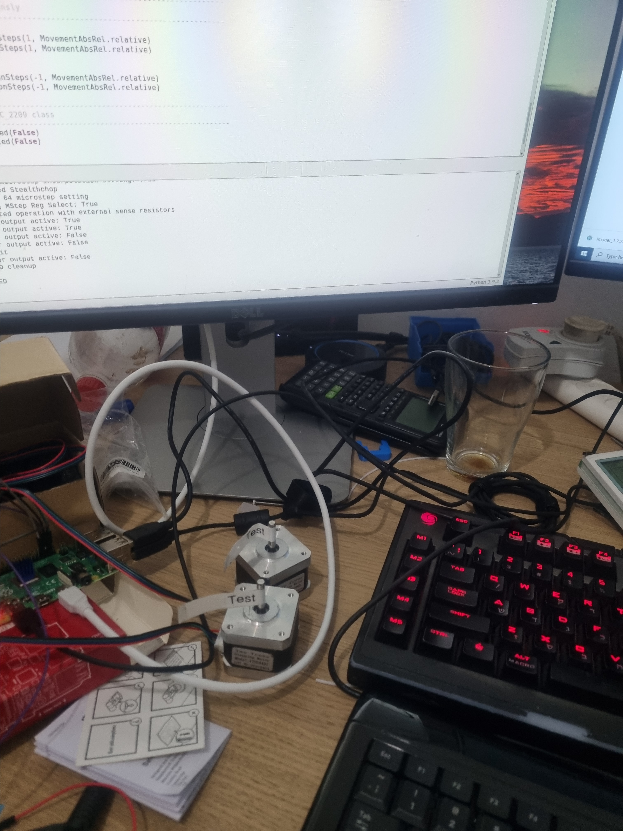
Imgaes/WIP/20220412_033123.jpg
