Yakir-Shlez/AutoChess/Imgaes/WIP/20220418_222432.jpg

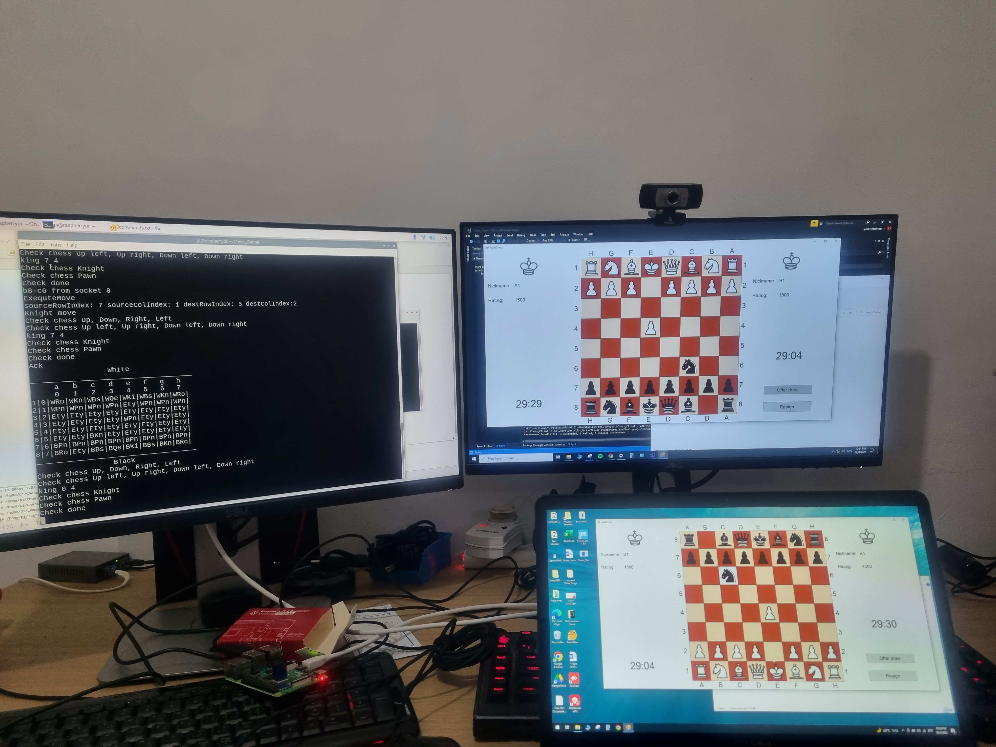
Imgaes/WIP/20220418_222432.jpg
