Yakir-Shlez/AutoChess/Imgaes/WIP/20220418_222456.jpg

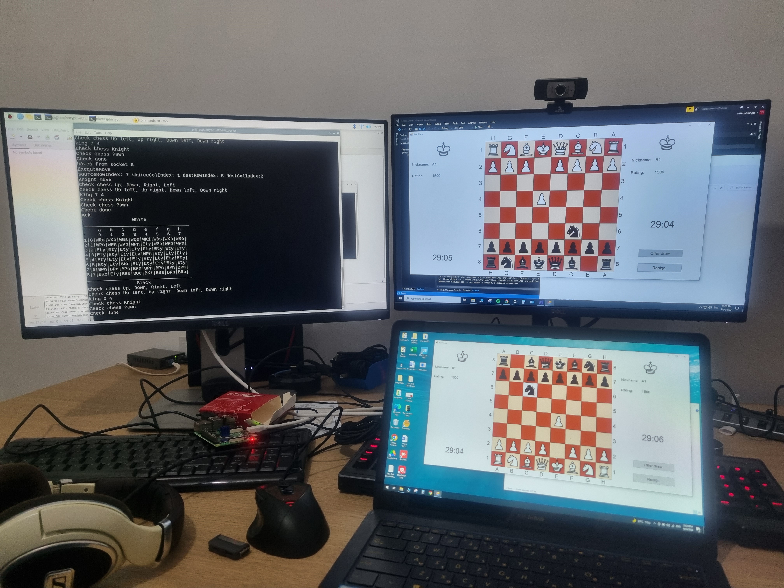
Imgaes/WIP/20220418_222456.jpg
