Yakir-Shlez/AutoChess/Imgaes/WIP/20220618_132042.jpg

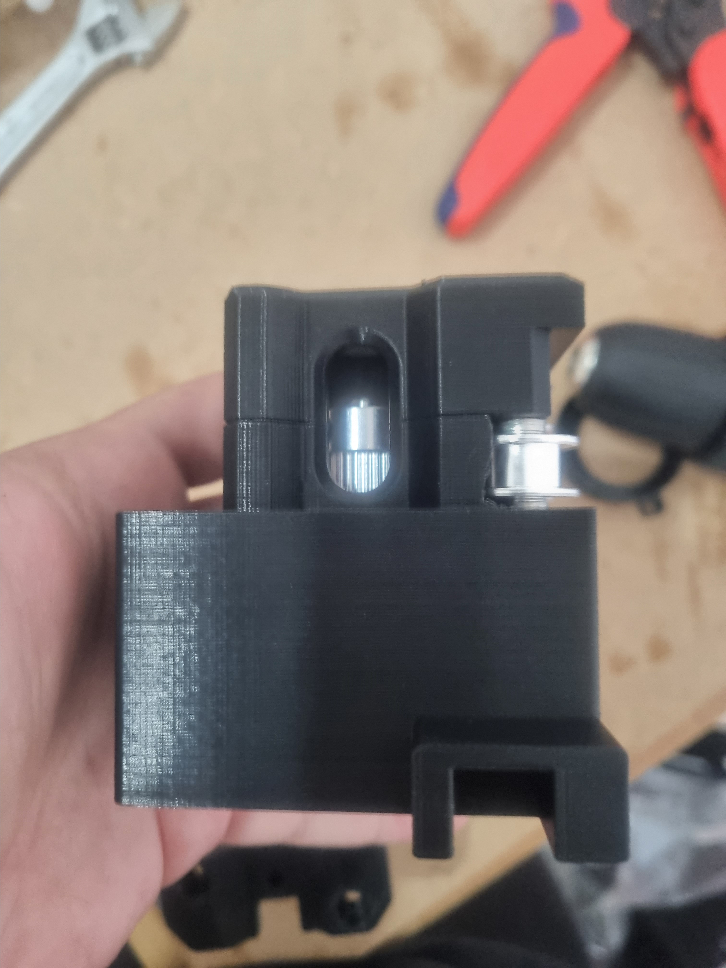
Imgaes/WIP/20220618_132042.jpg
