Yakir-Shlez/AutoChess/Imgaes/WIP/20220618_132046.jpg

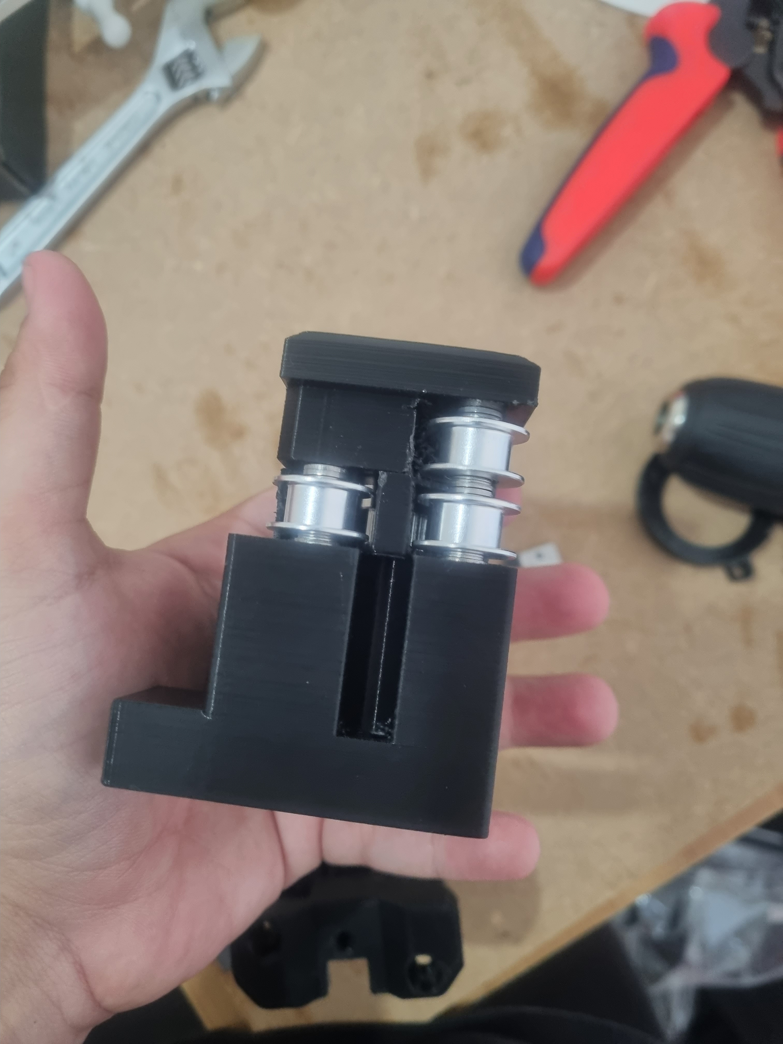
Imgaes/WIP/20220618_132046.jpg
