Yakir-Shlez/AutoChess/Imgaes/WIP/20220618_132053.jpg

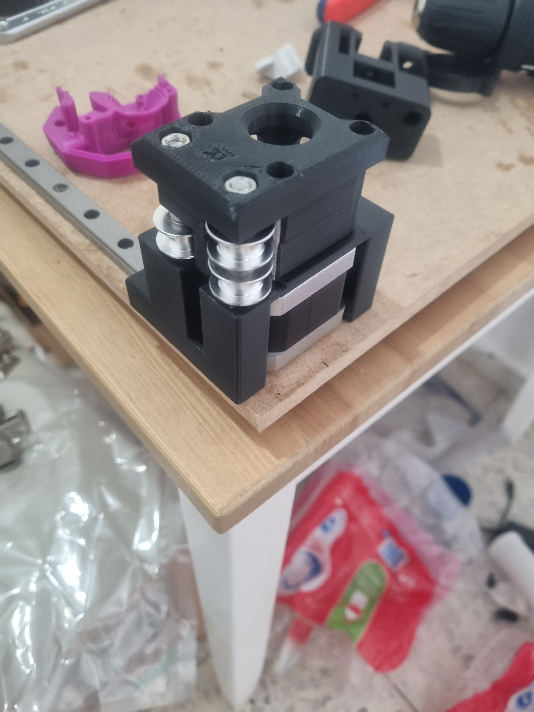
Imgaes/WIP/20220618_132053.jpg
