Yakir-Shlez/AutoChess/Imgaes/WIP/20220618_164856.jpg

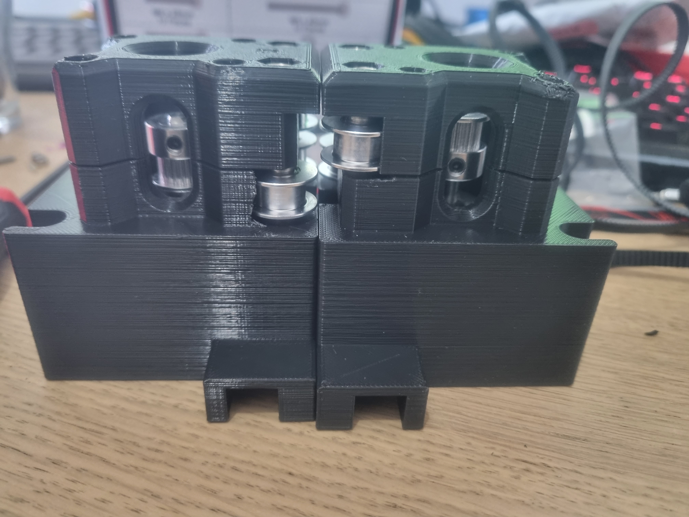
Imgaes/WIP/20220618_164856.jpg
