Yakir-Shlez/AutoChess/Imgaes/WIP/20220618_164906.jpg

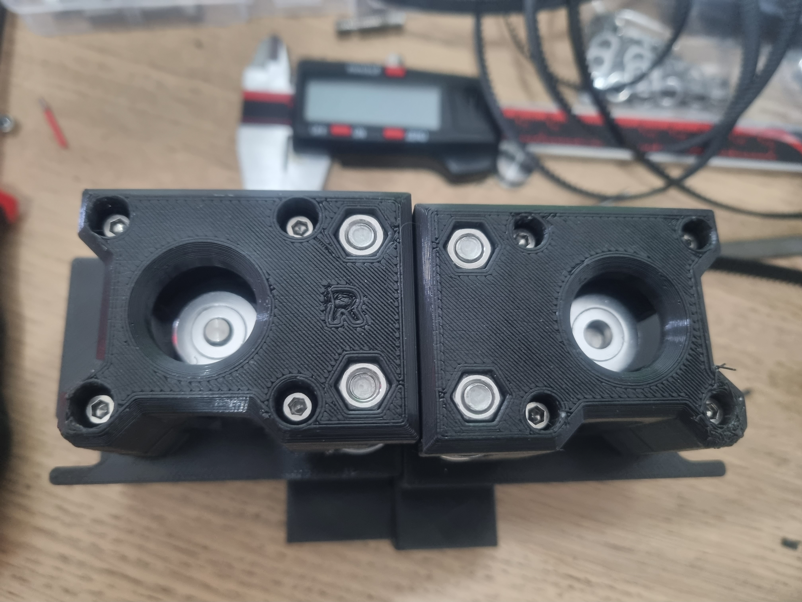
Imgaes/WIP/20220618_164906.jpg
