Yakir-Shlez/AutoChess/Imgaes/WIP/20220618_195724.jpg

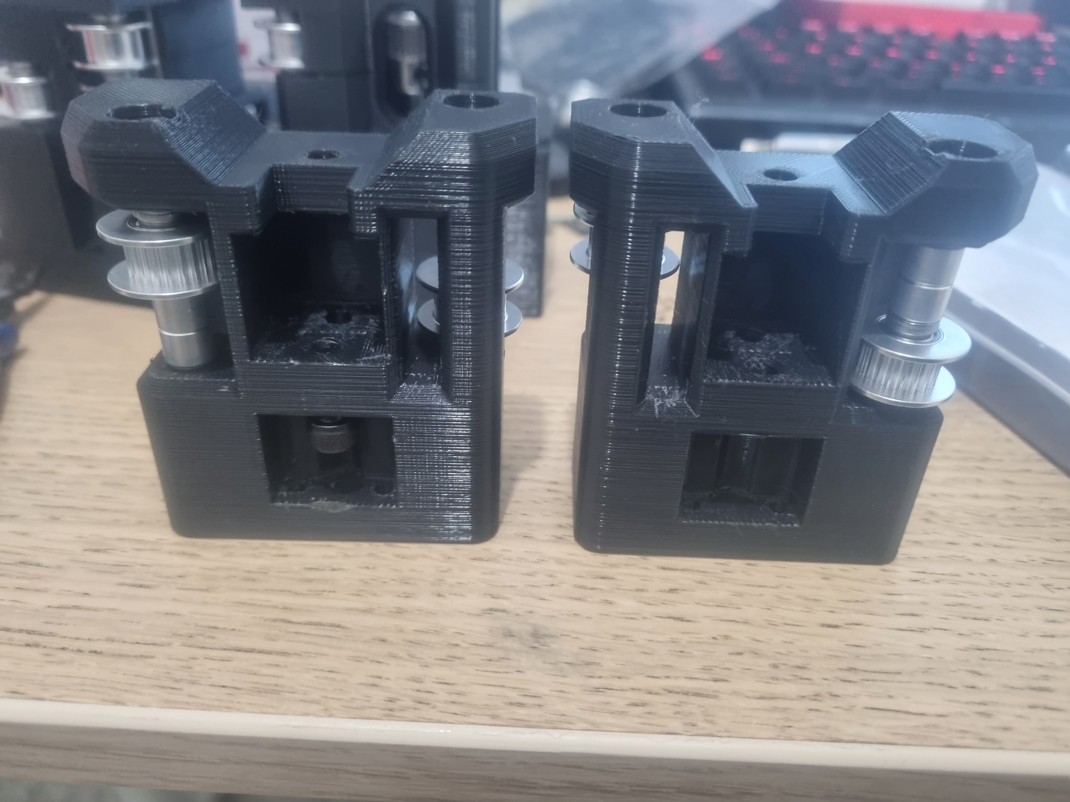
Imgaes/WIP/20220618_195724.jpg
