Yakir-Shlez/AutoChess/Imgaes/WIP/20220618_195733.jpg

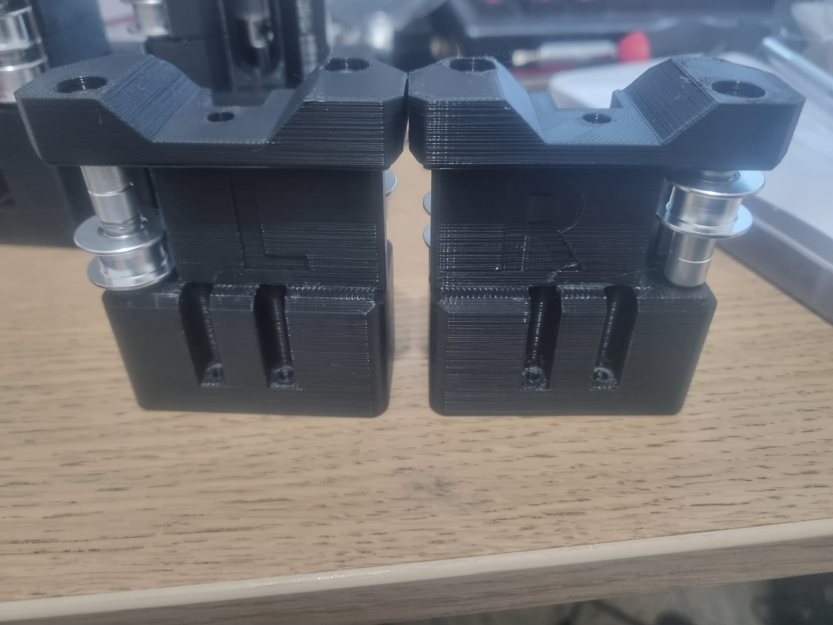
Imgaes/WIP/20220618_195733.jpg
