Yakir-Shlez/AutoChess/Imgaes/WIP/20220619_021702.jpg

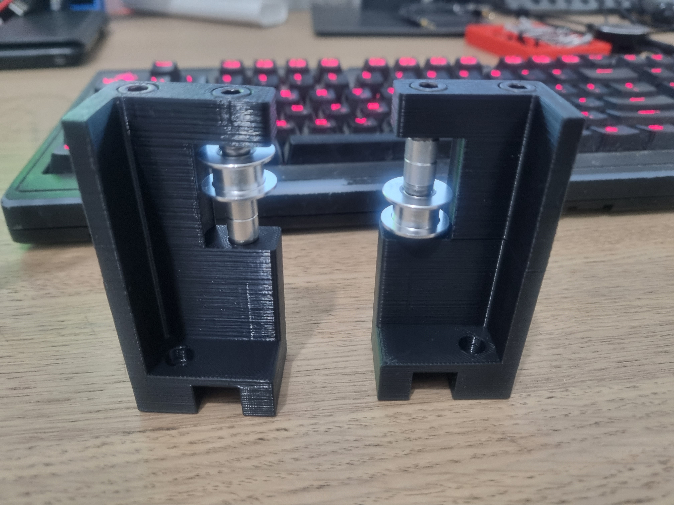
Imgaes/WIP/20220619_021702.jpg
