Yakir-Shlez/AutoChess/Imgaes/WIP/20220619_023346.jpg

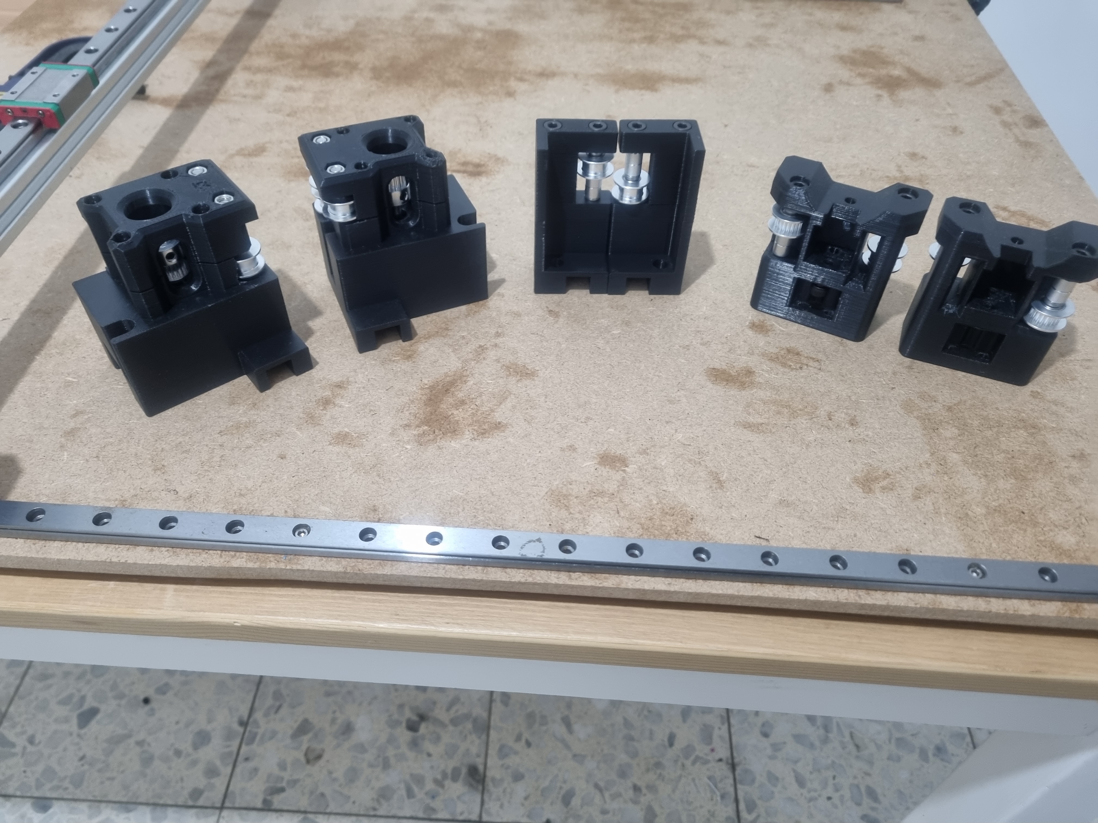
Imgaes/WIP/20220619_023346.jpg
