Yakir-Shlez/AutoChess/Imgaes/WIP/20220620_181037.jpg

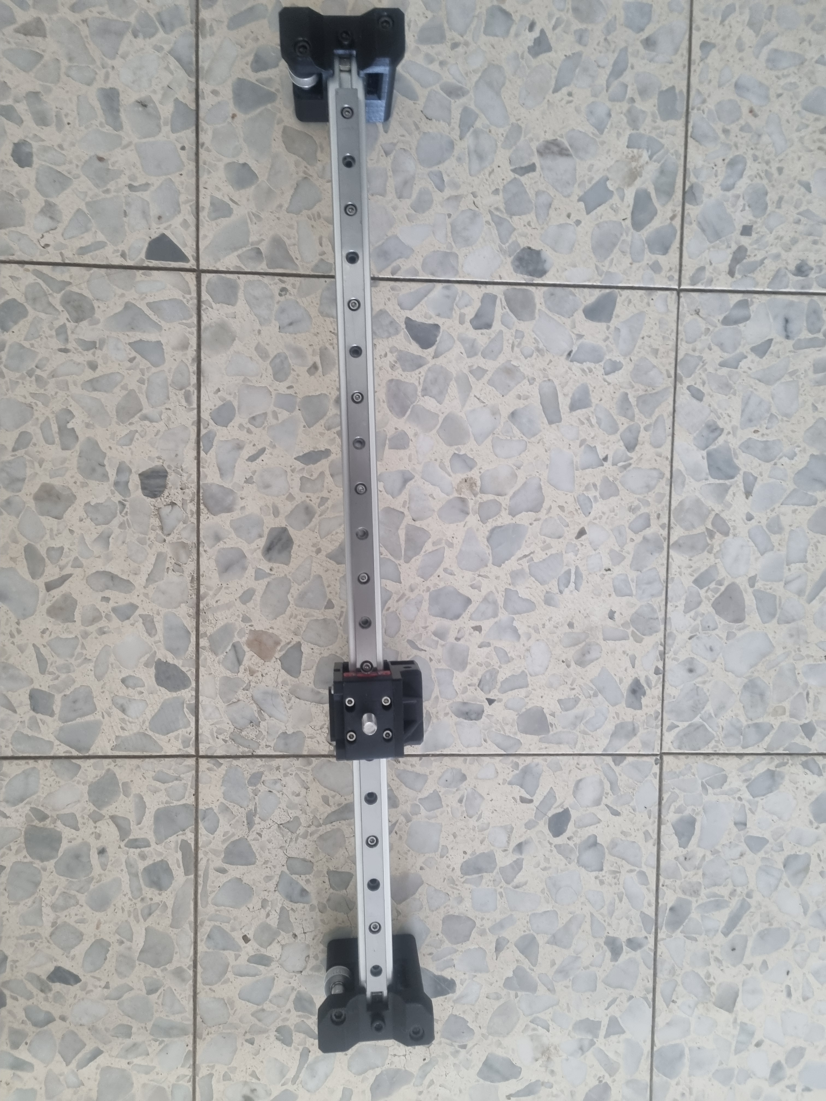
Imgaes/WIP/20220620_181037.jpg
