Yakir-Shlez/AutoChess/Imgaes/WIP/20220620_201059.jpg

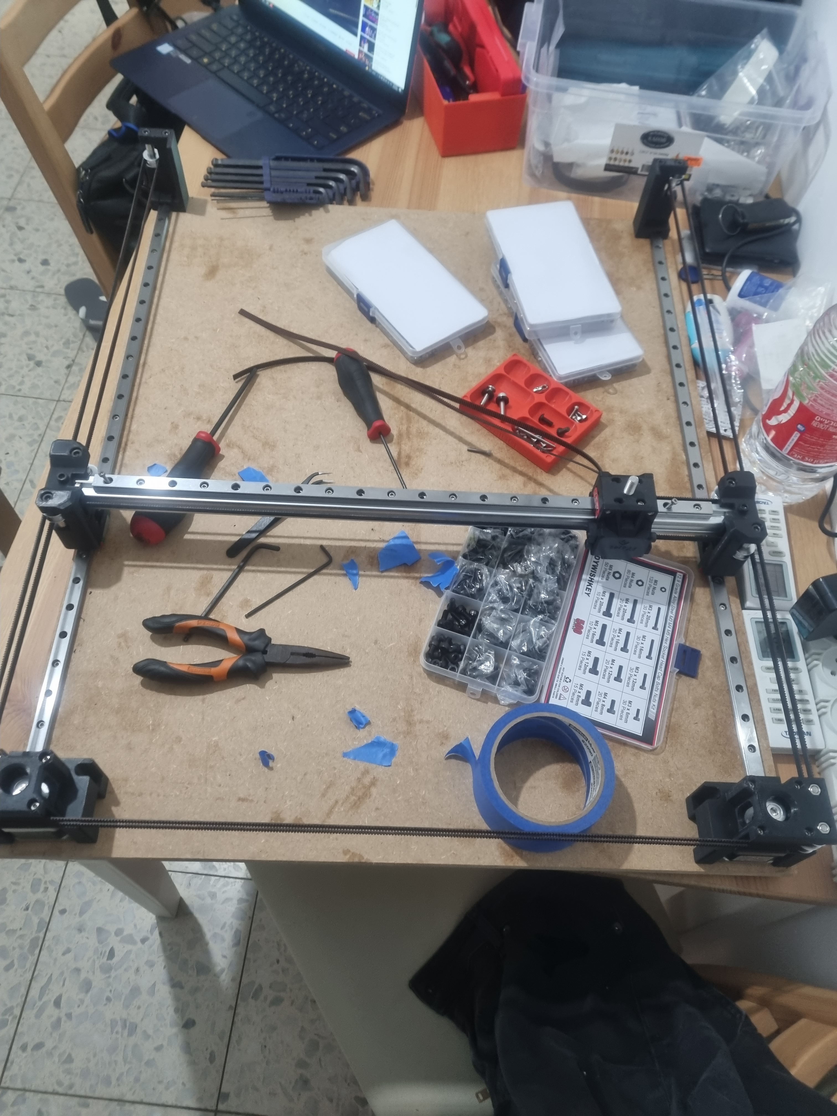
Imgaes/WIP/20220620_201059.jpg
