Yakir-Shlez/AutoChess/Imgaes/WIP/20220620_201358.jpg

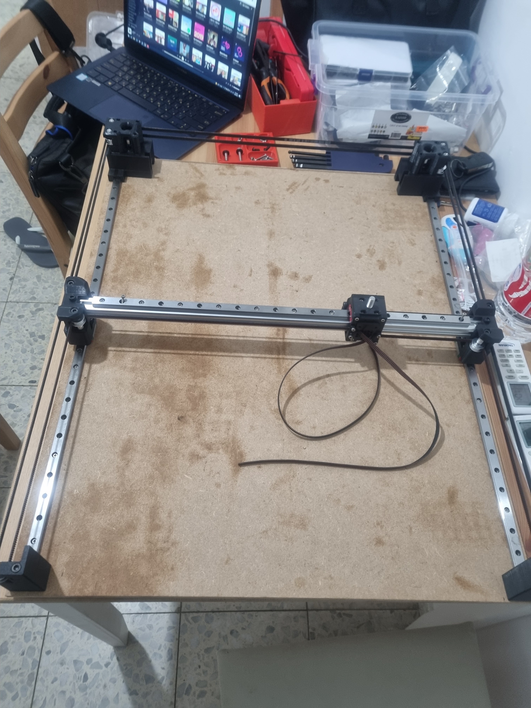
Imgaes/WIP/20220620_201358.jpg
