Yakir-Shlez/AutoChess/Imgaes/WIP/20220620_203440.jpg

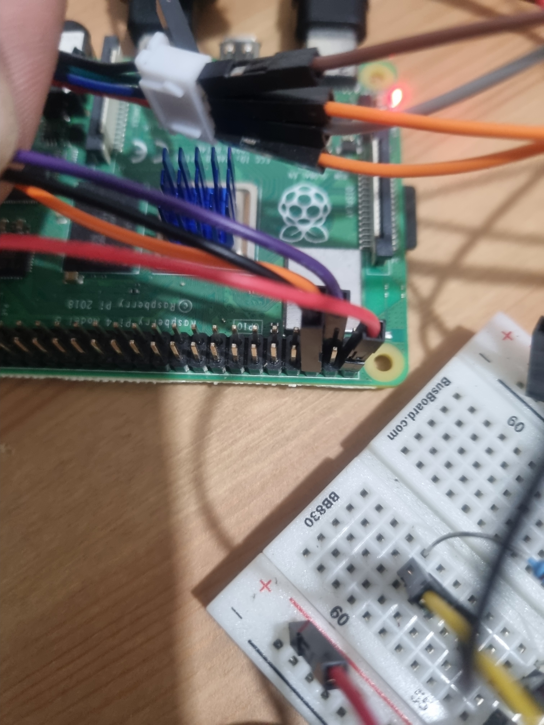
Imgaes/WIP/20220620_203440.jpg
