Yakir-Shlez/AutoChess/Imgaes/WIP/20220620_203442.jpg

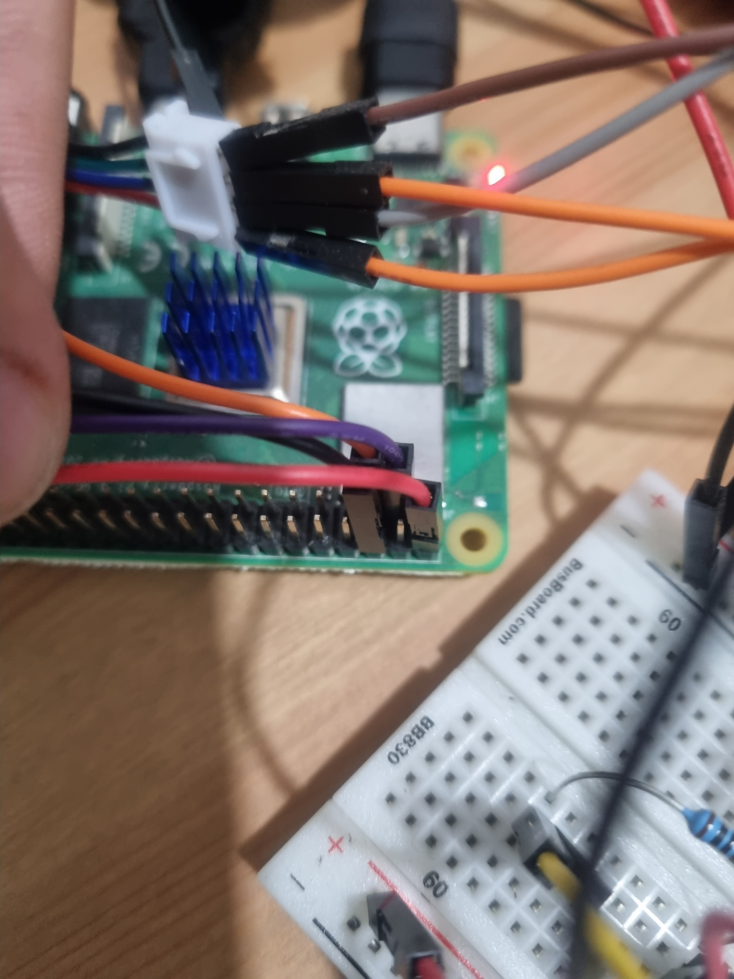
Imgaes/WIP/20220620_203442.jpg
