Yakir-Shlez/AutoChess/Imgaes/WIP/20220620_203445.jpg

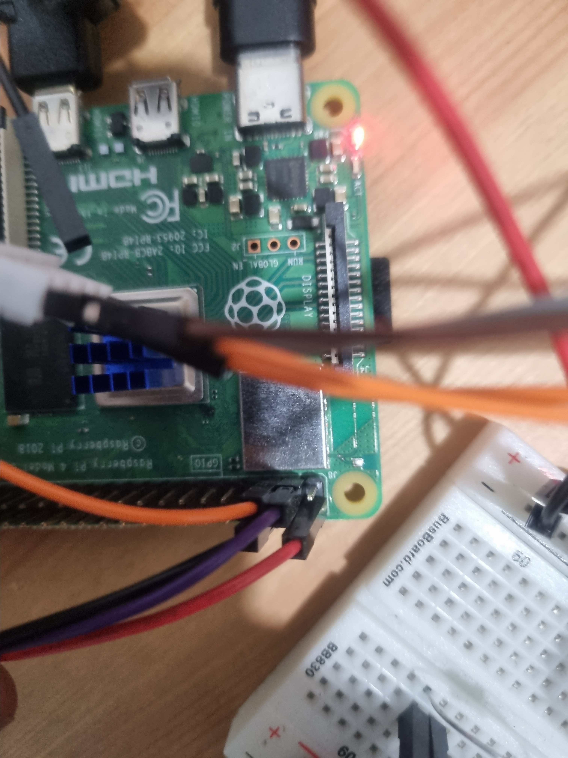
Imgaes/WIP/20220620_203445.jpg
