Yakir-Shlez/AutoChess/Imgaes/WIP/20220720_051406.jpg

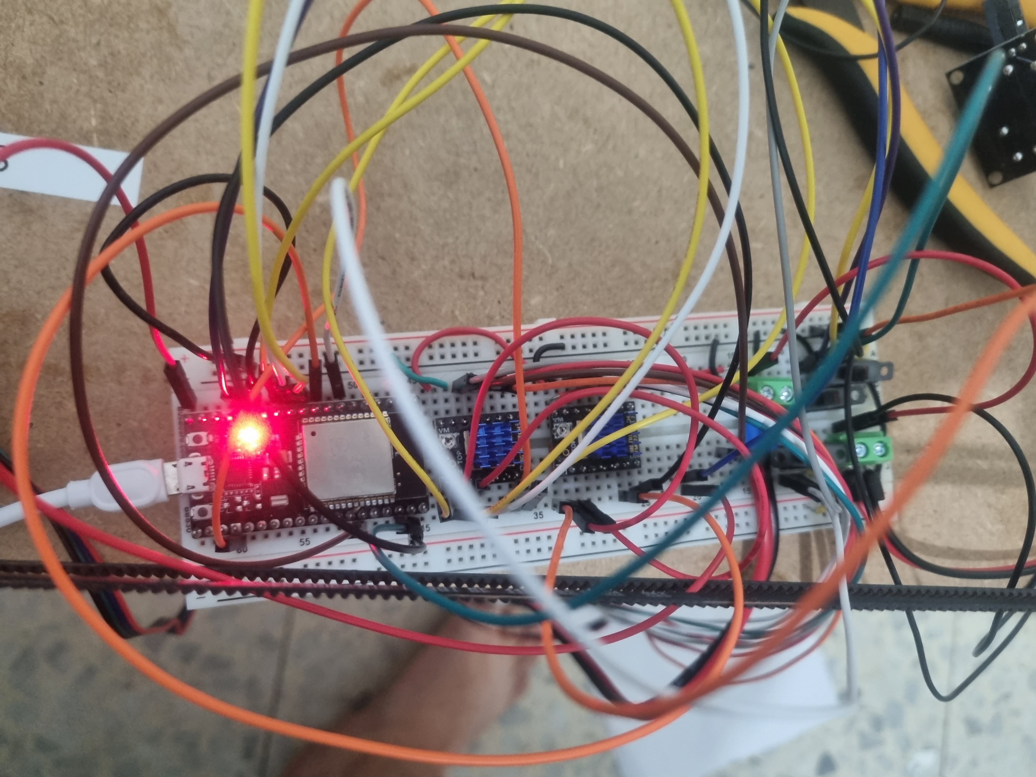
Imgaes/WIP/20220720_051406.jpg
