Yakir-Shlez/AutoChess/Imgaes/WIP/20220728_205928.jpg

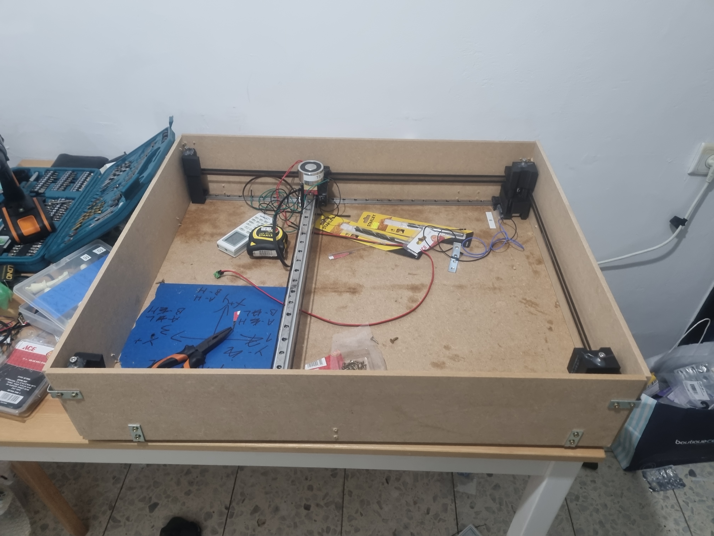
Imgaes/WIP/20220728_205928.jpg
