Yakir-Shlez/AutoChess/Imgaes/WIP/20220728_205947.jpg

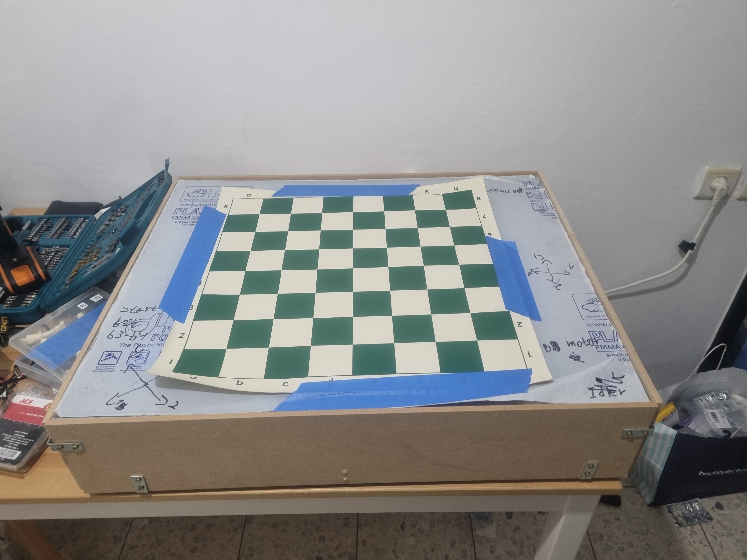
Imgaes/WIP/20220728_205947.jpg
