Yakir-Shlez/AutoChess/Imgaes/WIP/20220731_185159.jpg

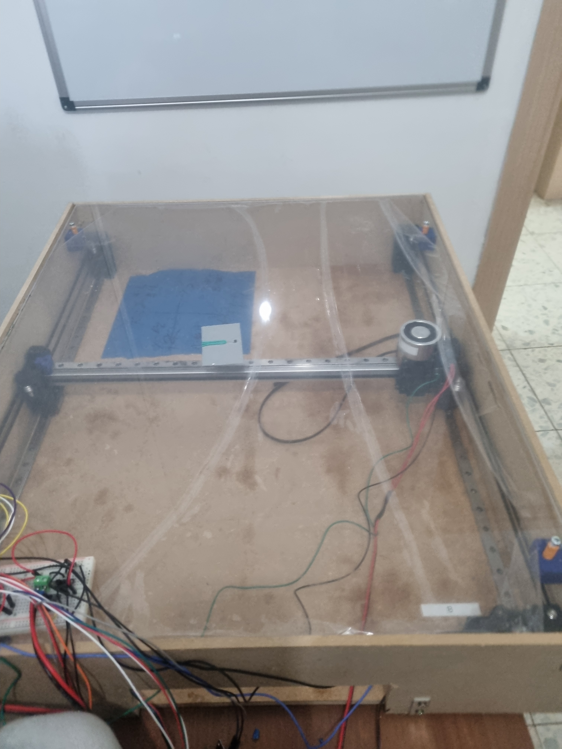
Imgaes/WIP/20220731_185159.jpg
