Yakir-Shlez/AutoChess/Imgaes/WIP/20220731_203059.jpg

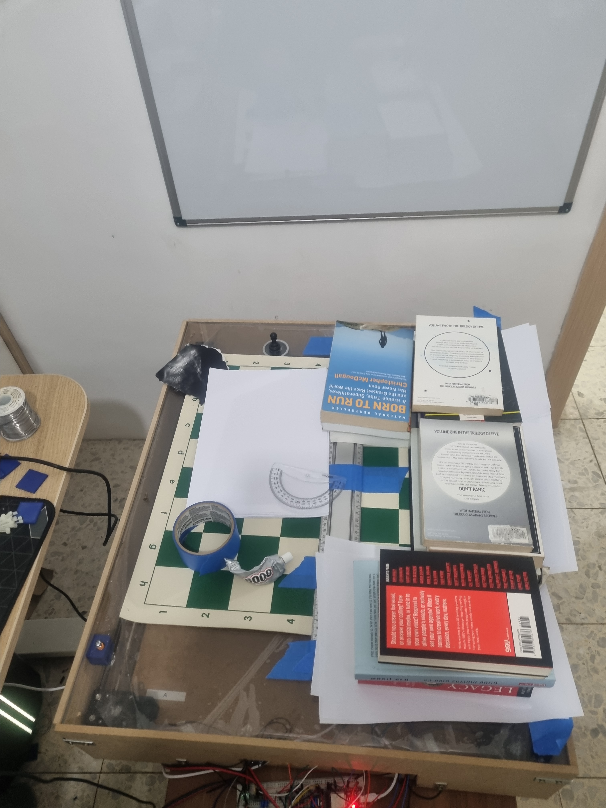
Imgaes/WIP/20220731_203059.jpg
