Yakir-Shlez/AutoChess/Imgaes/WIP/20220903_224112.jpg

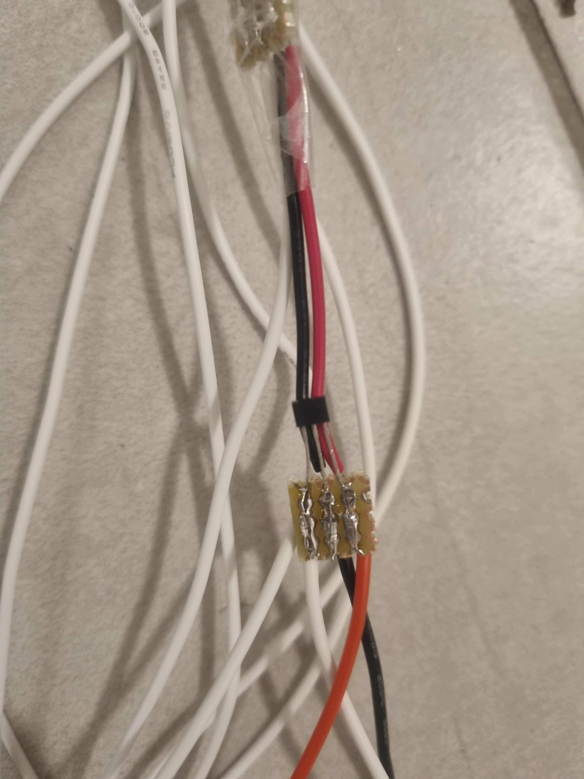
Imgaes/WIP/20220903_224112.jpg
