Yakir-Shlez/AutoChess/Imgaes/WIP/20220904_035513.jpg

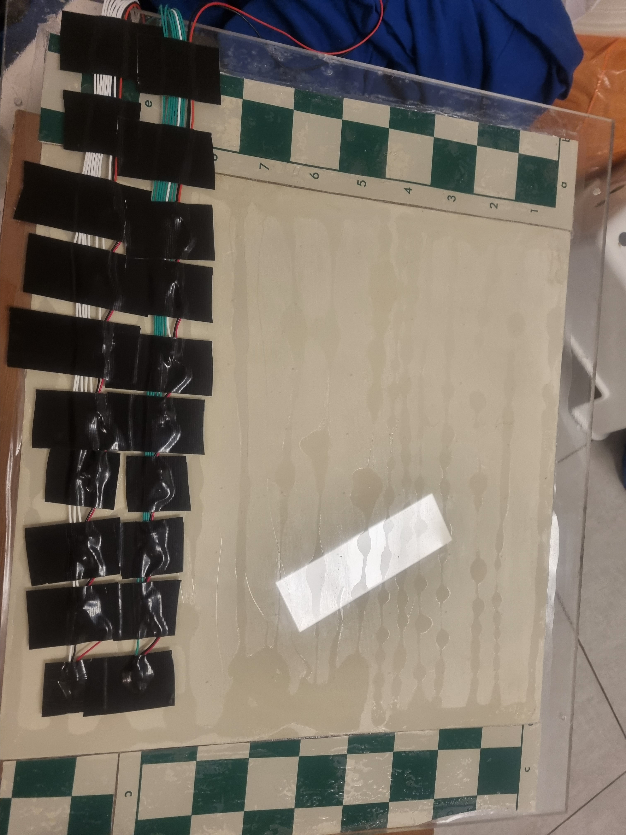
Imgaes/WIP/20220904_035513.jpg
