Yakir-Shlez/AutoChess/Imgaes/WIP/20220911_170606.jpg

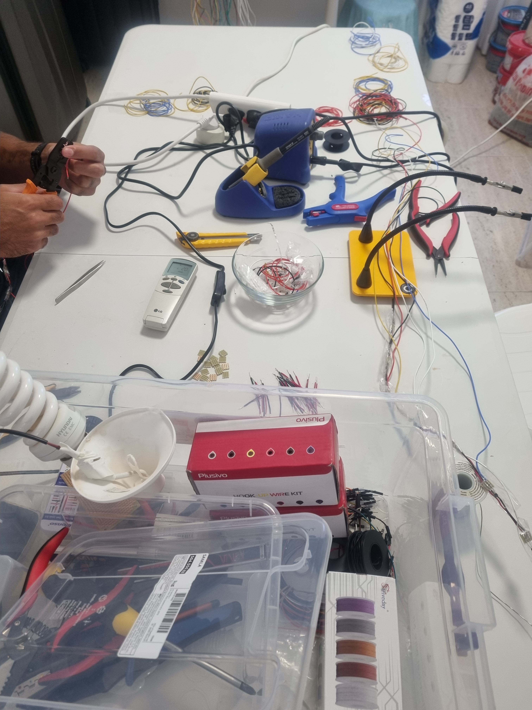
Imgaes/WIP/20220911_170606.jpg
