Yakir-Shlez/AutoChess/Imgaes/WIP/20220911_170617.jpg

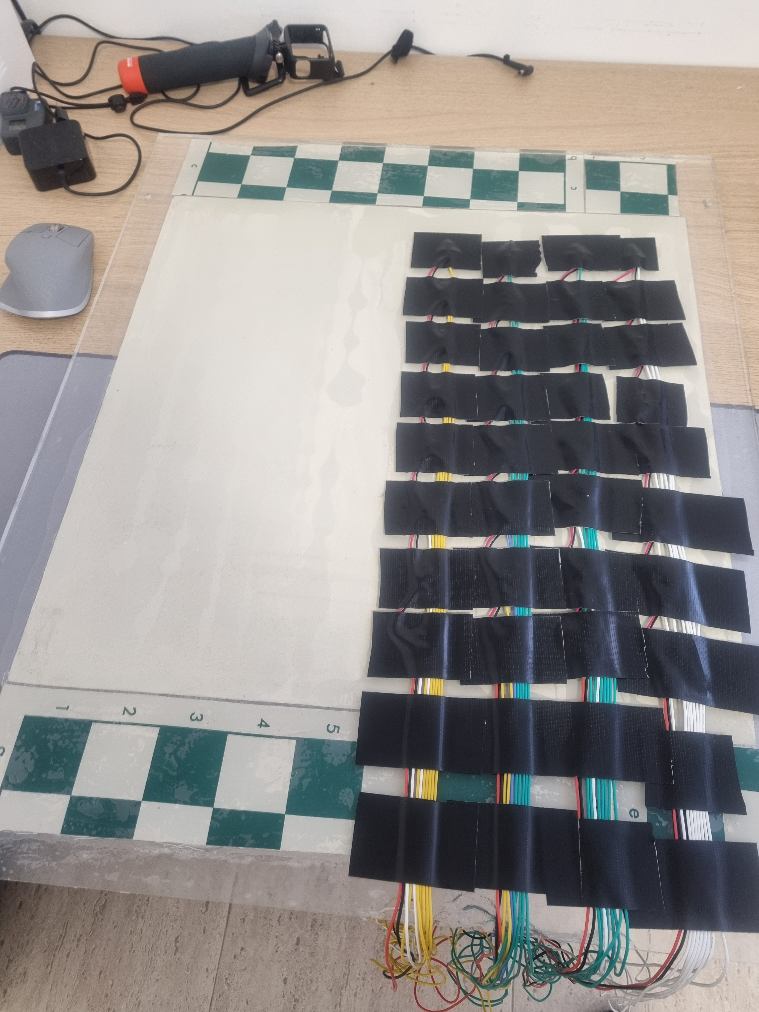
Imgaes/WIP/20220911_170617.jpg
