Yakir-Shlez/AutoChess/Imgaes/WIP/20220911_183419.jpg

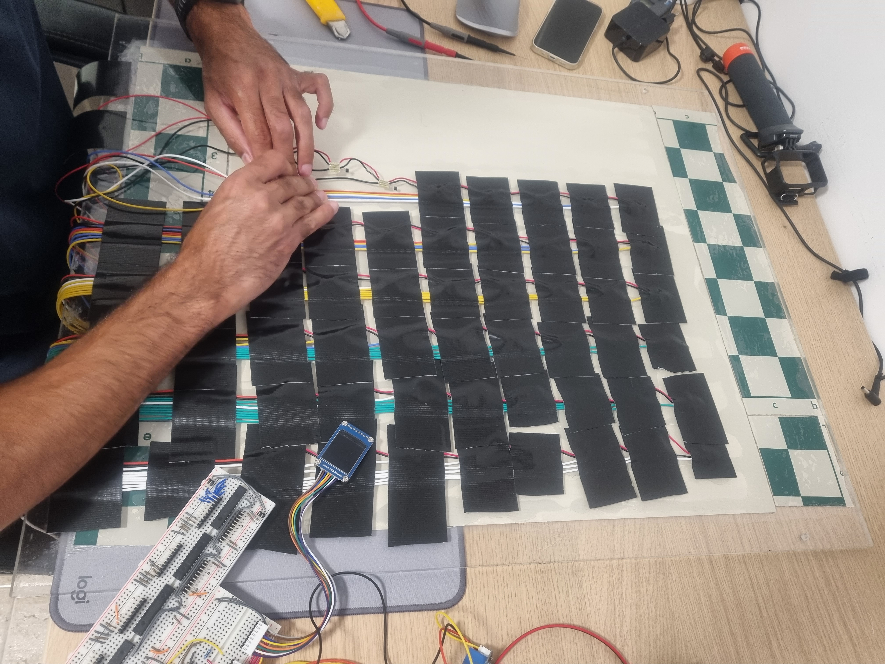
Imgaes/WIP/20220911_183419.jpg
