Yakir-Shlez/AutoChess/Imgaes/WIP/20220911_230010.jpg

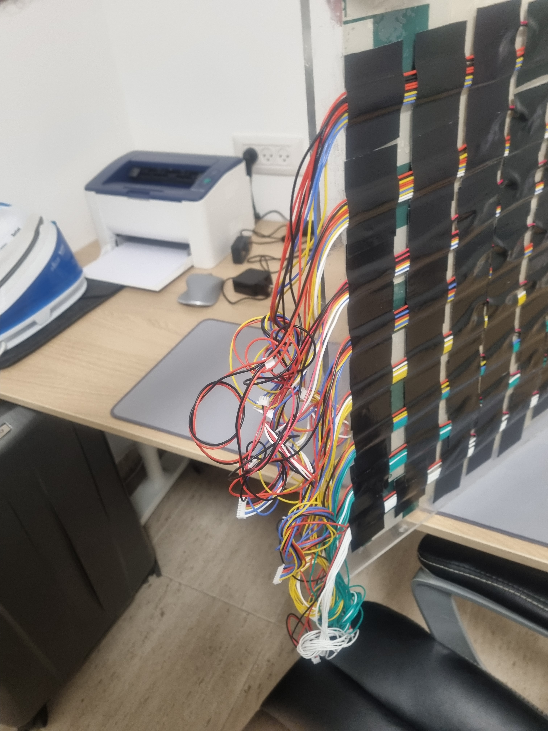
Imgaes/WIP/20220911_230010.jpg
