Yakir-Shlez/AutoChess/Imgaes/WIP/20220914_051813.jpg

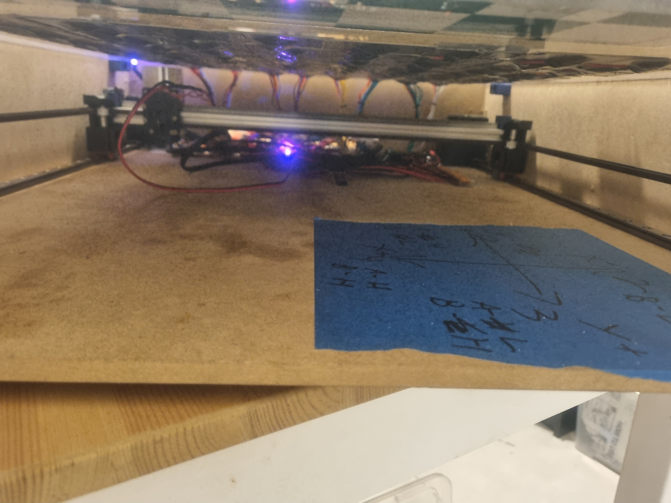
Imgaes/WIP/20220914_051813.jpg
