Yakir-Shlez/AutoChess/Imgaes/WIP/20220914_052116.jpg

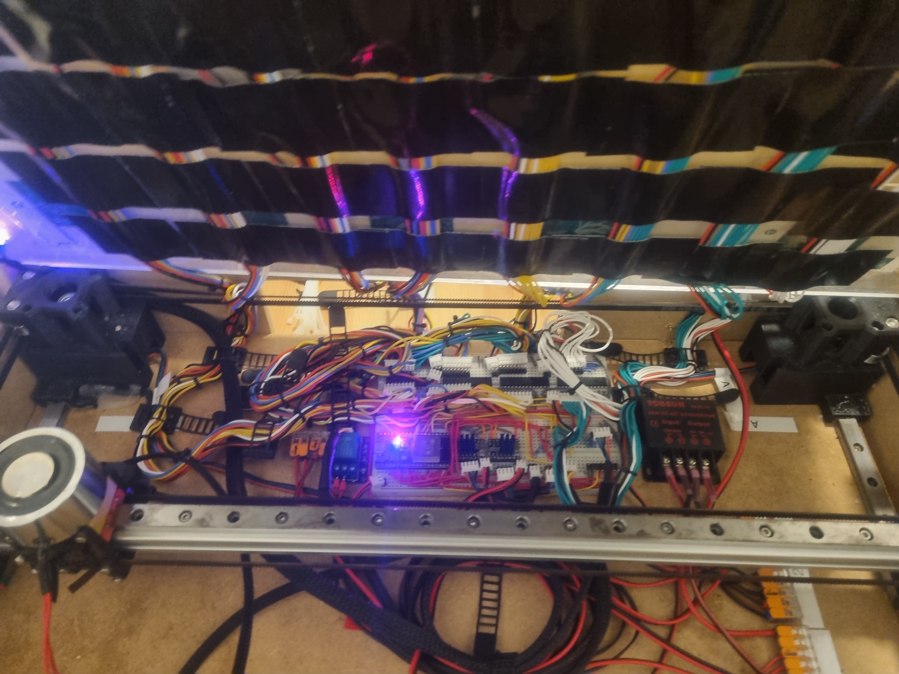
Imgaes/WIP/20220914_052116.jpg
