Yakir-Shlez/AutoChess/Imgaes/WIP/20220918_232850.jpg

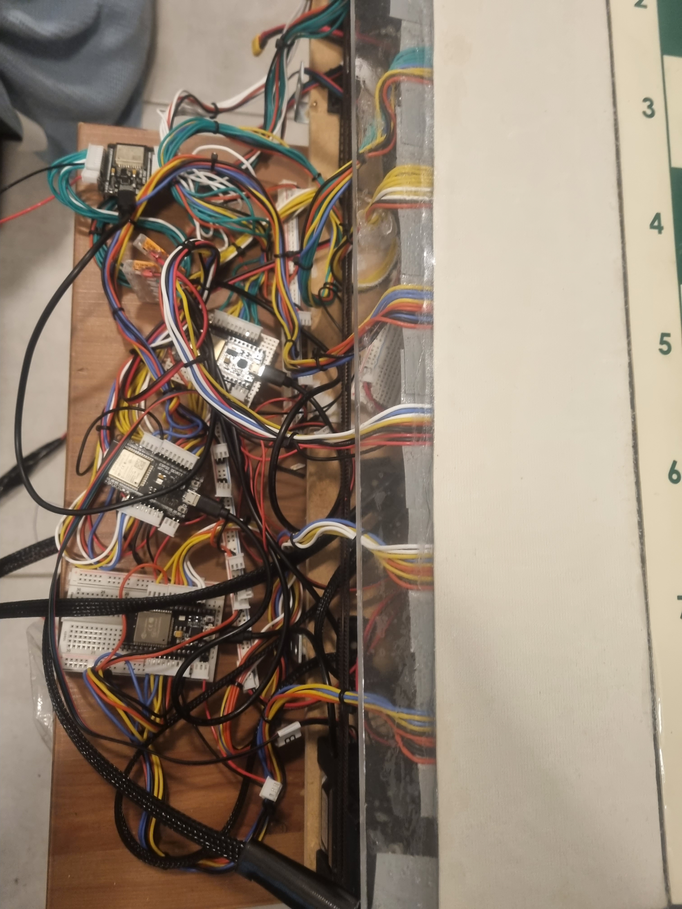
Imgaes/WIP/20220918_232850.jpg
