Yakir-Shlez/AutoChess/Board/STL/Spring_Holder.stl

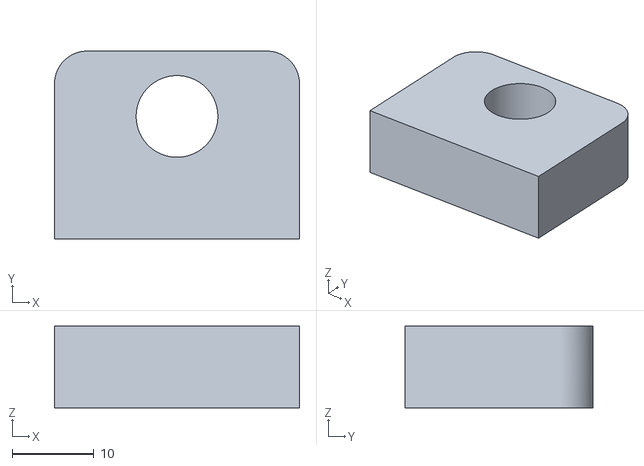
[picture p120: CAD file, 2022-08-23]
Board/STL/Spring_Holder.stl
30.0 x 23.0 x 10.0
