Yakir-Shlez/AutoChess/Board/STL/top_mgn12.stl

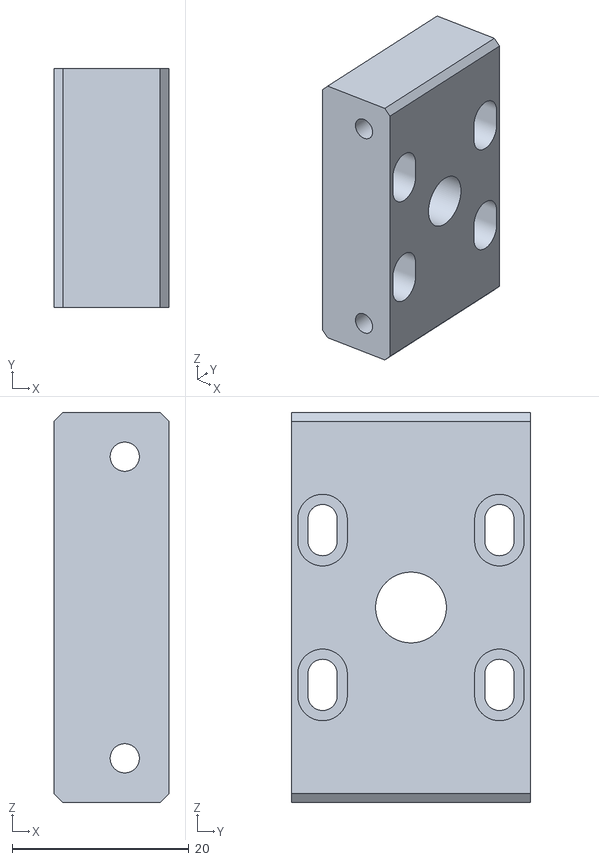
[picture p121: CAD file, 2022-08-23]
Board/STL/top_mgn12.stl
13.0 x 27.0 x 44.1
