Yakir-Shlez/AutoChess/Board/STL/xy_joiner_left.stl

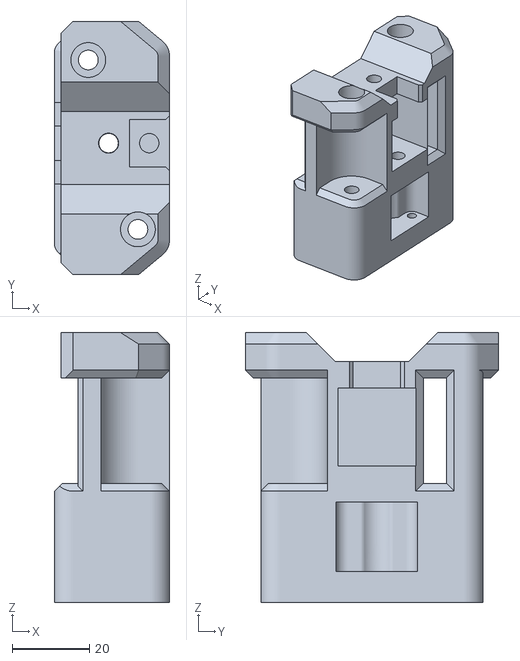
[picture p122: CAD file, 2022-08-23]
Board/STL/xy_joiner_left.stl
29.8 x 65.5 x 69.8
