Yakir-Shlez/AutoChess/Board/STL/Idler_Plate_Left.stl

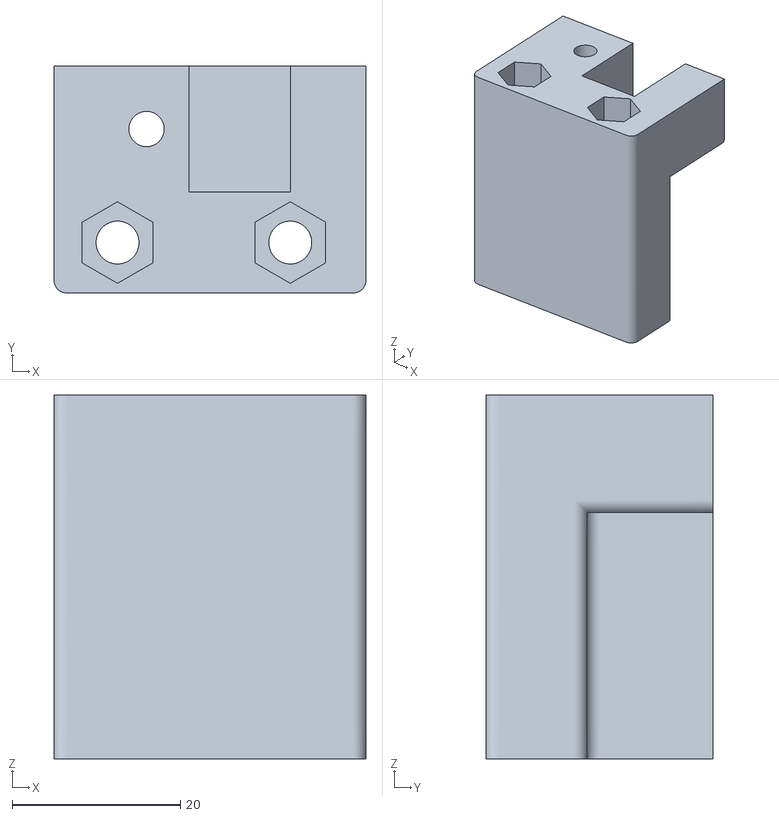
[picture p123: CAD file, 2022-08-23]
Board/STL/Idler_Plate_Left.stl
37.1 x 27.0 x 43.3
