Yakir-Shlez/AutoChess/Board/STL/xy_joiner_right.stl

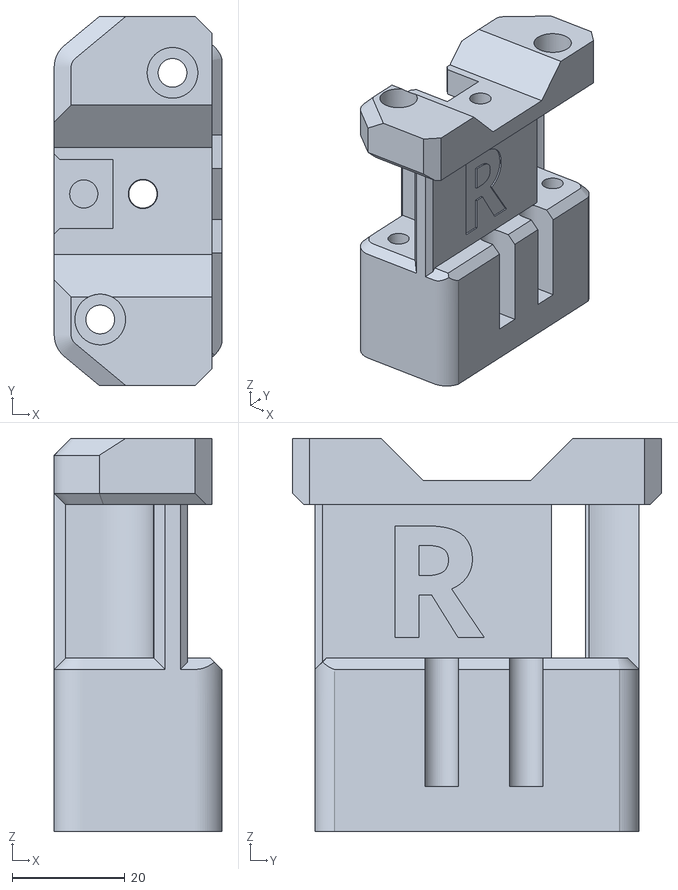
[picture p124: CAD file, 2022-08-23]
Board/STL/xy_joiner_right.stl
29.8 x 65.5 x 69.8
