Yakir-Shlez/AutoChess/Board/STL/xy_motor_cage_bottom_left.stl

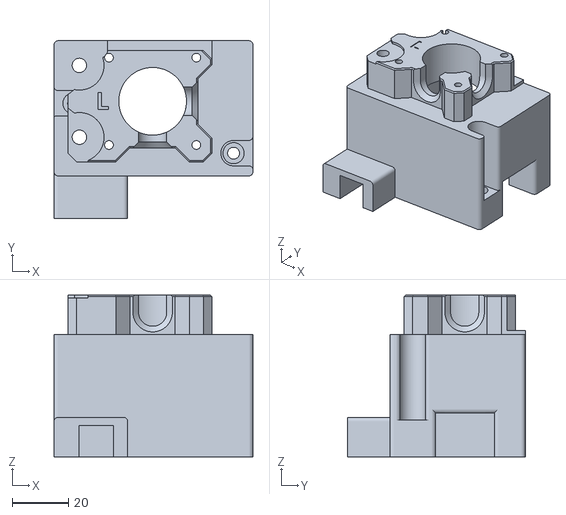
[picture p125: CAD file, 2022-08-23]
Board/STL/xy_motor_cage_bottom_left.stl
70.6 x 63.0 x 57.3
