Yakir-Shlez/AutoChess/Board/STL/Board_Holder v6.stl

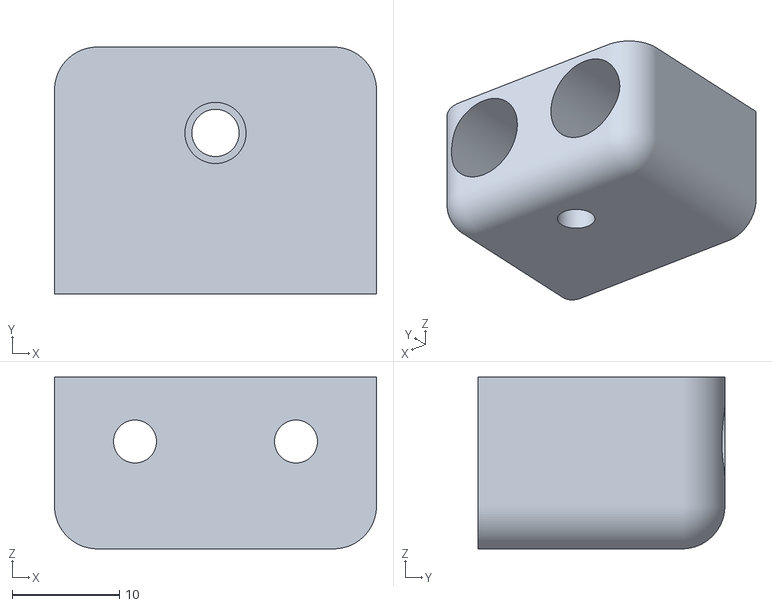
[picture p126: CAD file, 2022-08-23]
Board/STL/Board_Holder v6.stl
30.0 x 23.0 x 16.0
