Yakir-Shlez/AutoChess/Board/STL/face_belt_grabber.stl

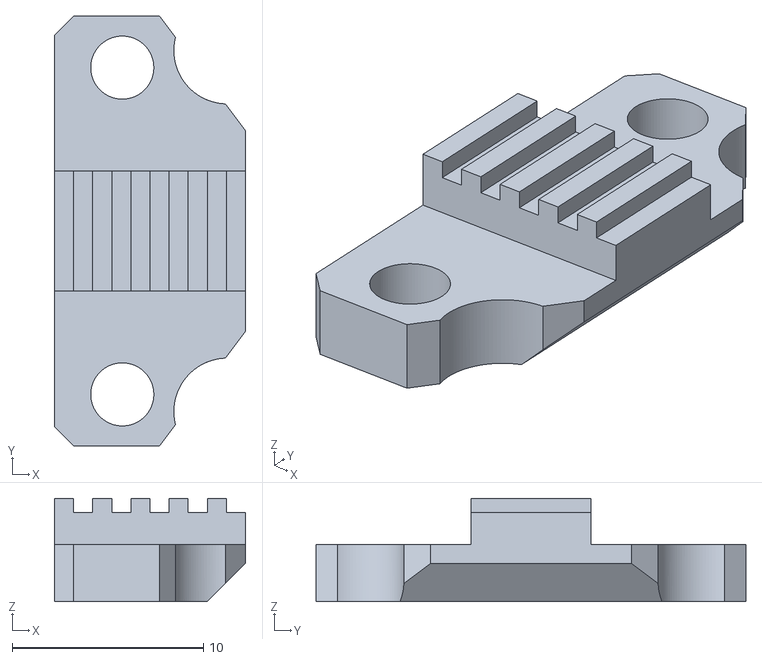
[picture p127: CAD file, 2022-08-23]
Board/STL/face_belt_grabber.stl
10.00 x 22.5 x 5.40
