Yakir-Shlez/AutoChess/Imgaes/WIP/20210816_194423.jpg

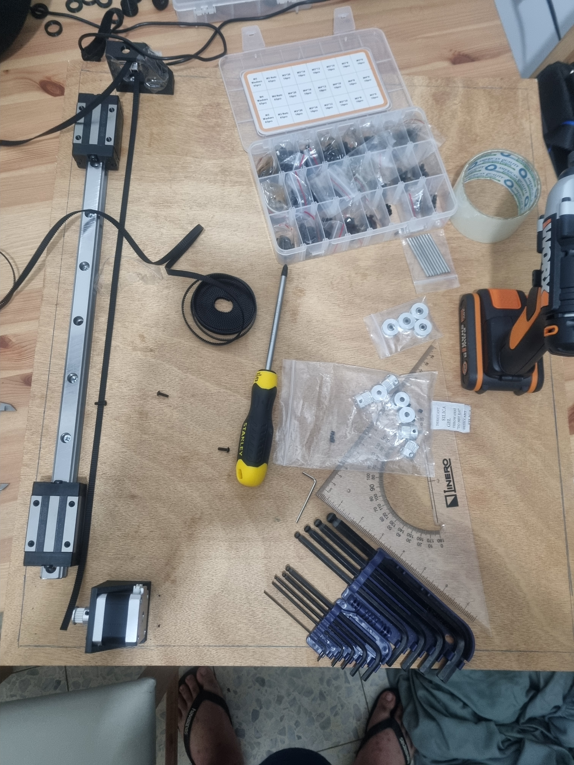
Imgaes/WIP/20210816_194423.jpg
