Yakir-Shlez/AutoChess/Imgaes/WIP/20220408_192029.jpg

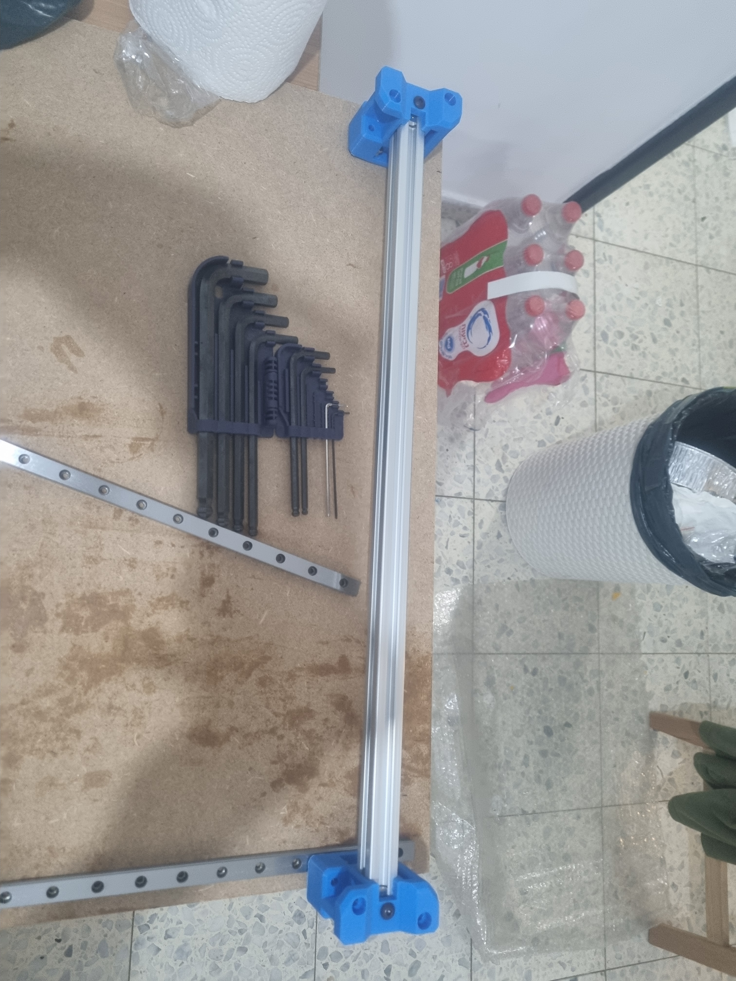
Imgaes/WIP/20220408_192029.jpg
