Yakir-Shlez/AutoChess/Imgaes/WIP/20220408_194543.jpg

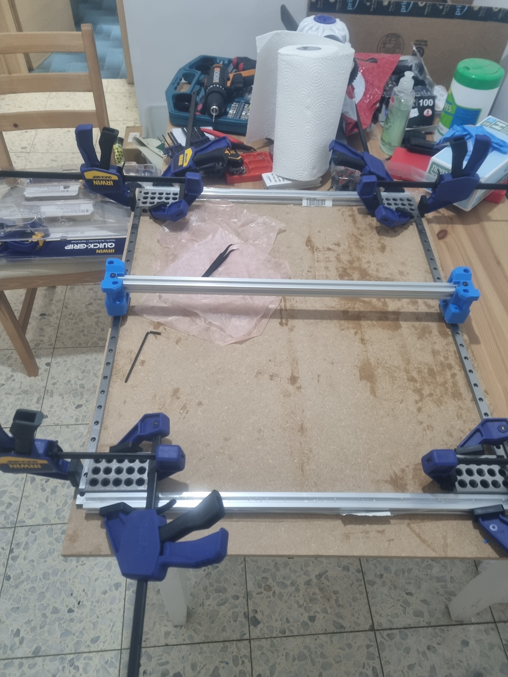
Imgaes/WIP/20220408_194543.jpg
