Yakir-Shlez/AutoChess/Imgaes/WIP/20220408_194550.jpg

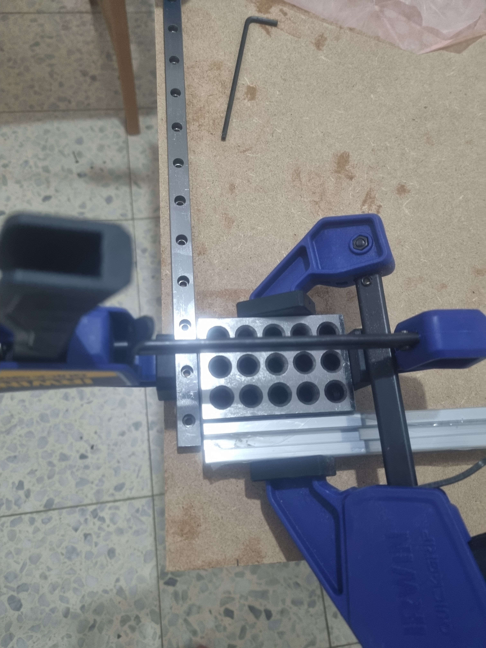
Imgaes/WIP/20220408_194550.jpg
