Yakir-Shlez/AutoChess/Imgaes/WIP/20220620_201400.jpg

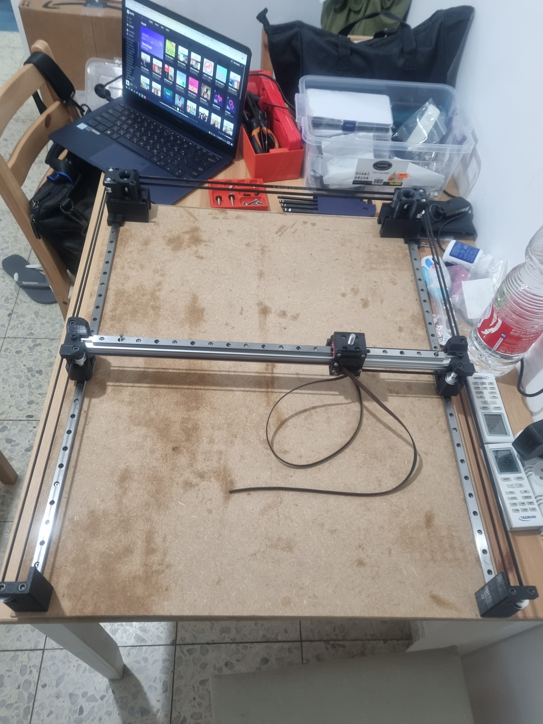
Imgaes/WIP/20220620_201400.jpg
