Yakir-Shlez/AutoChess/Imgaes/WIP/20220621_012057.jpg

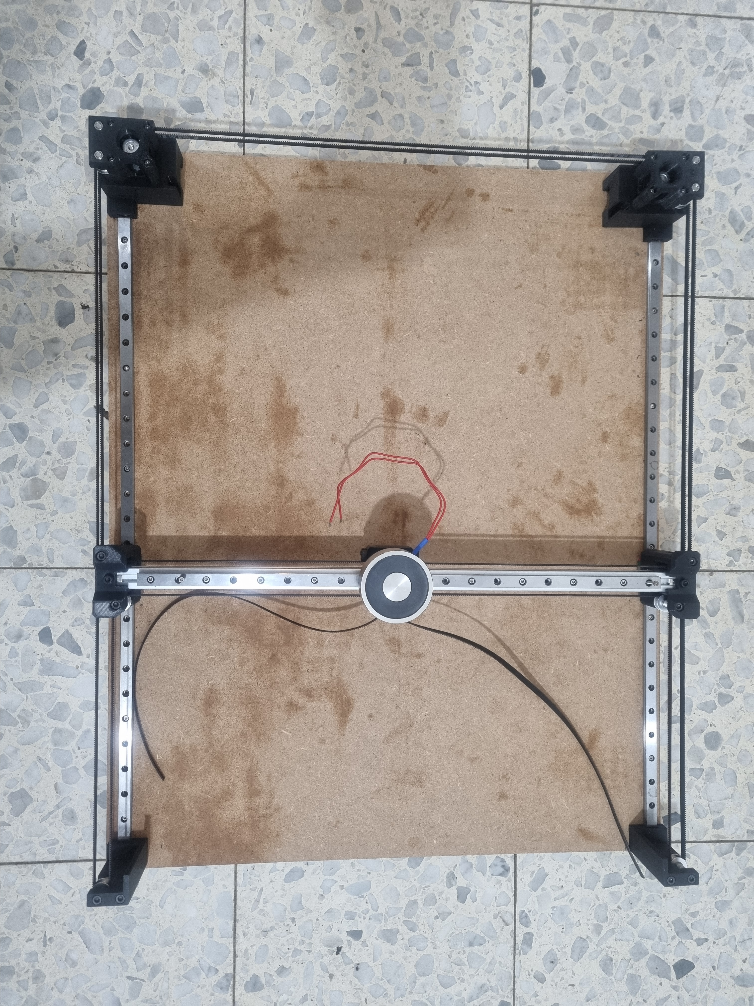
Imgaes/WIP/20220621_012057.jpg
