Yakir-Shlez/AutoChess/Imgaes/WIP/20220621_012104.jpg

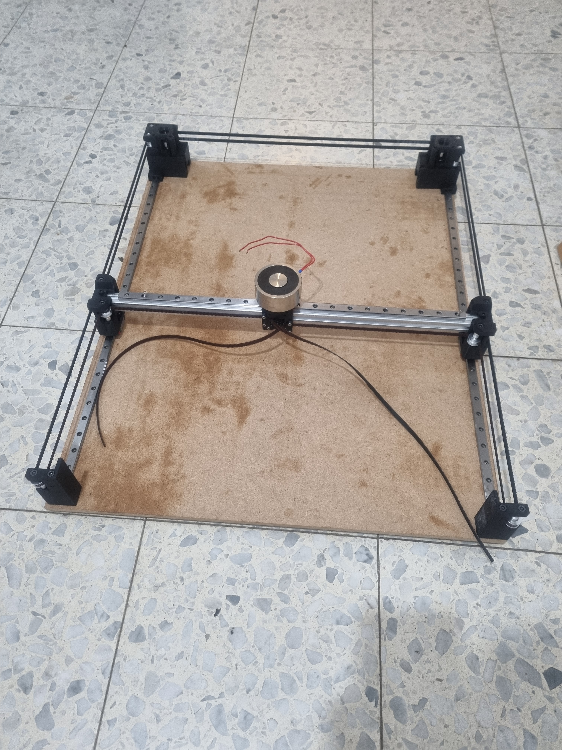
Imgaes/WIP/20220621_012104.jpg
