Yakir-Shlez/AutoChess/Imgaes/WIP/20220621_012111.jpg

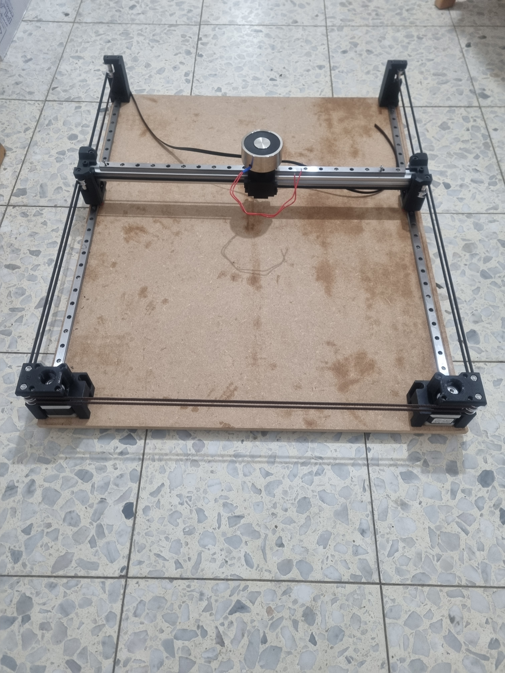
Imgaes/WIP/20220621_012111.jpg
