Yakir-Shlez/AutoChess/Imgaes/WIP/20220720_051357.jpg

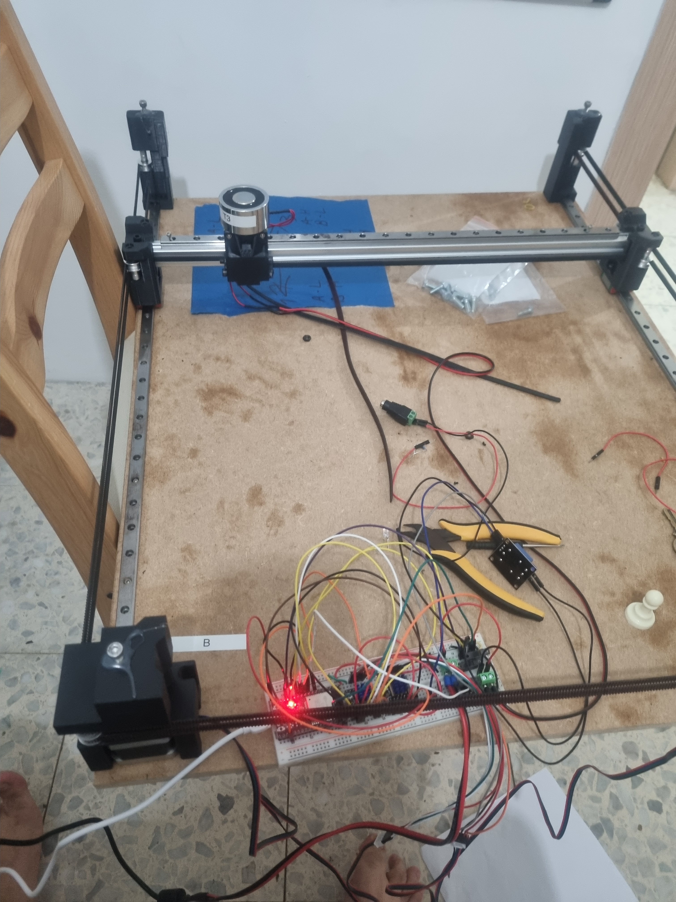
Imgaes/WIP/20220720_051357.jpg
