Yakir-Shlez/AutoChess/Imgaes/WIP/20220731_200354.jpg

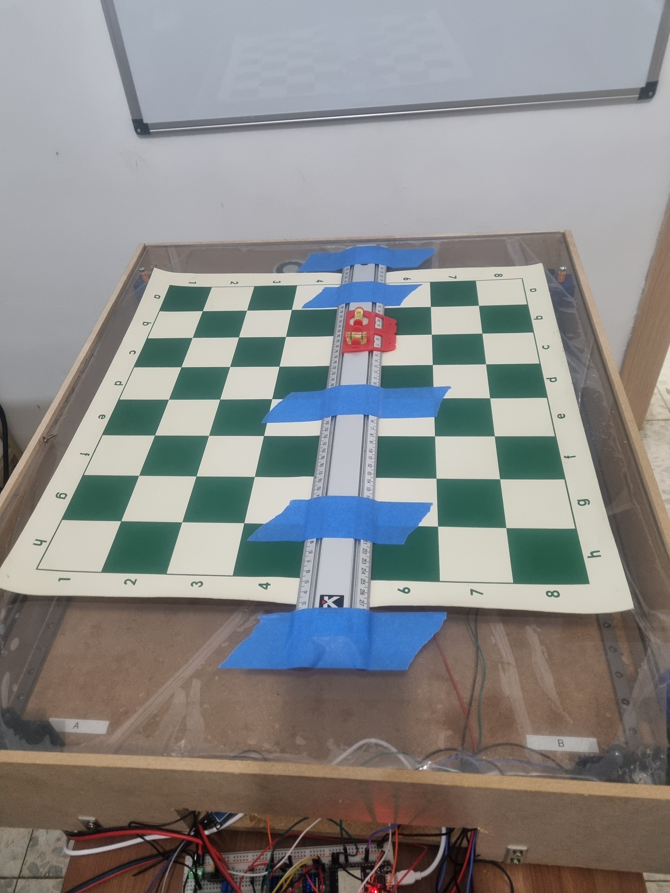
Imgaes/WIP/20220731_200354.jpg
