Yakir-Shlez/AutoChess/Imgaes/WIP/20220903_145110.jpg

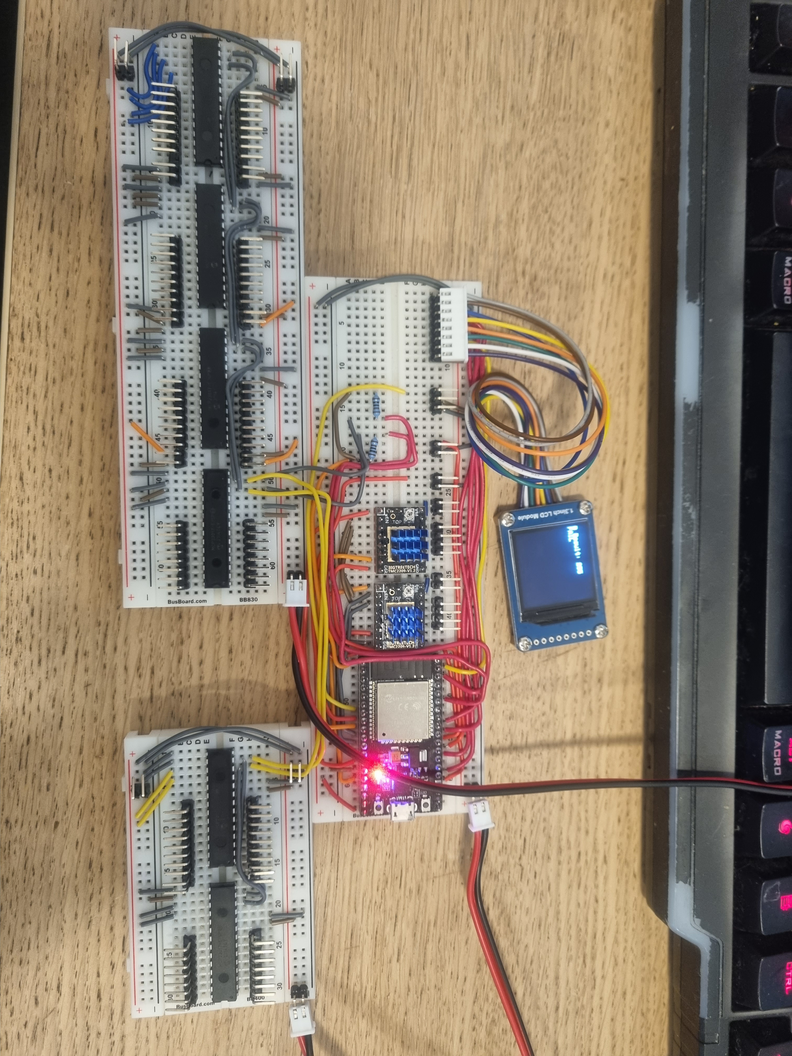
Imgaes/WIP/20220903_145110.jpg
