Yakir-Shlez/AutoChess/Imgaes/WIP/20220903_224102.jpg

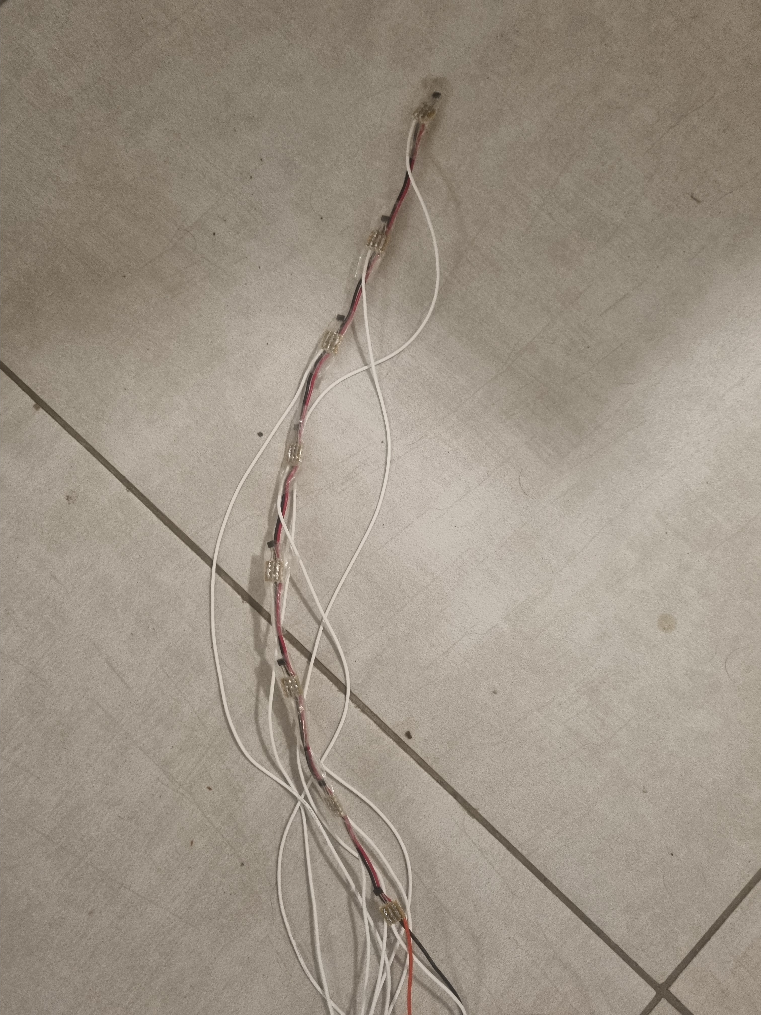
Imgaes/WIP/20220903_224102.jpg
