Yakir-Shlez/AutoChess/Imgaes/WIP/20220911_225924.jpg

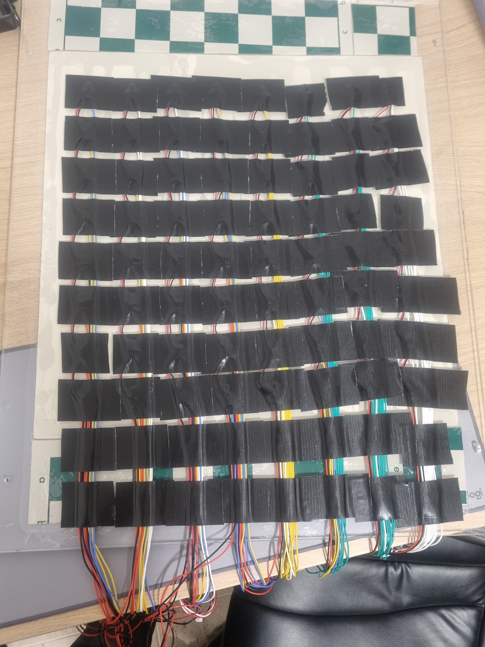
Imgaes/WIP/20220911_225924.jpg
