Yakir-Shlez/AutoChess/Imgaes/WIP/20220913_034408.jpg

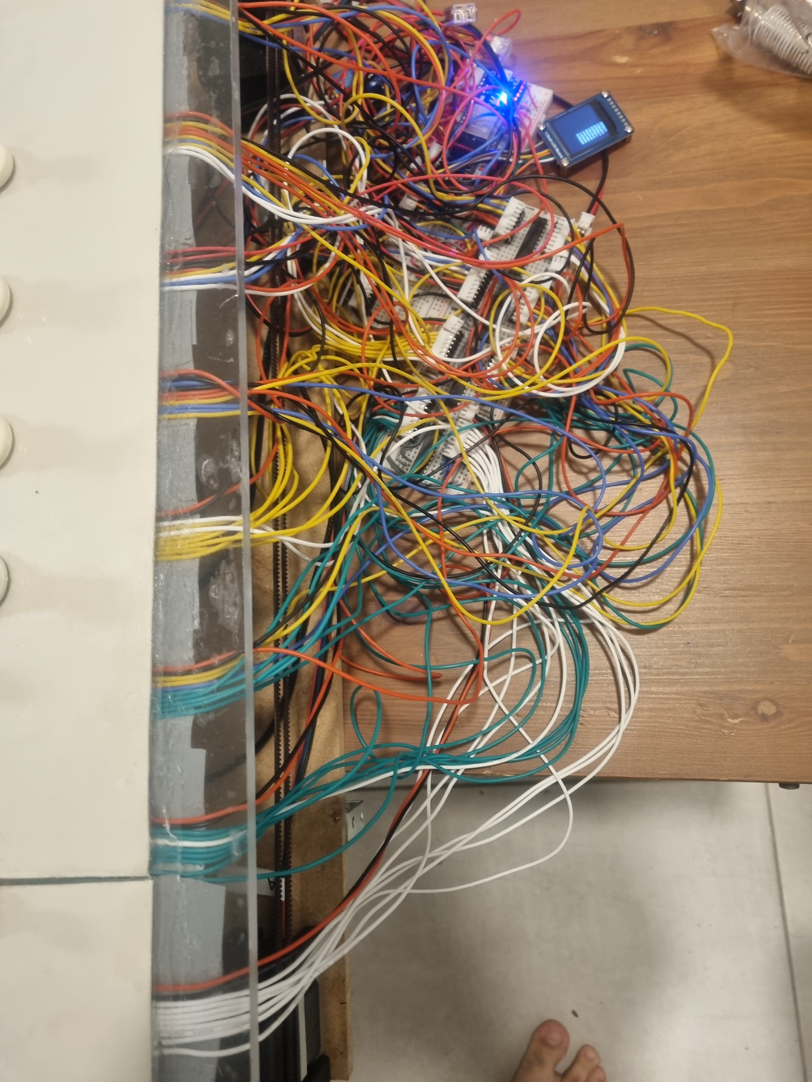
Imgaes/WIP/20220913_034408.jpg
