Yakir-Shlez/AutoChess/Imgaes/WIP/20220914_021122.jpg

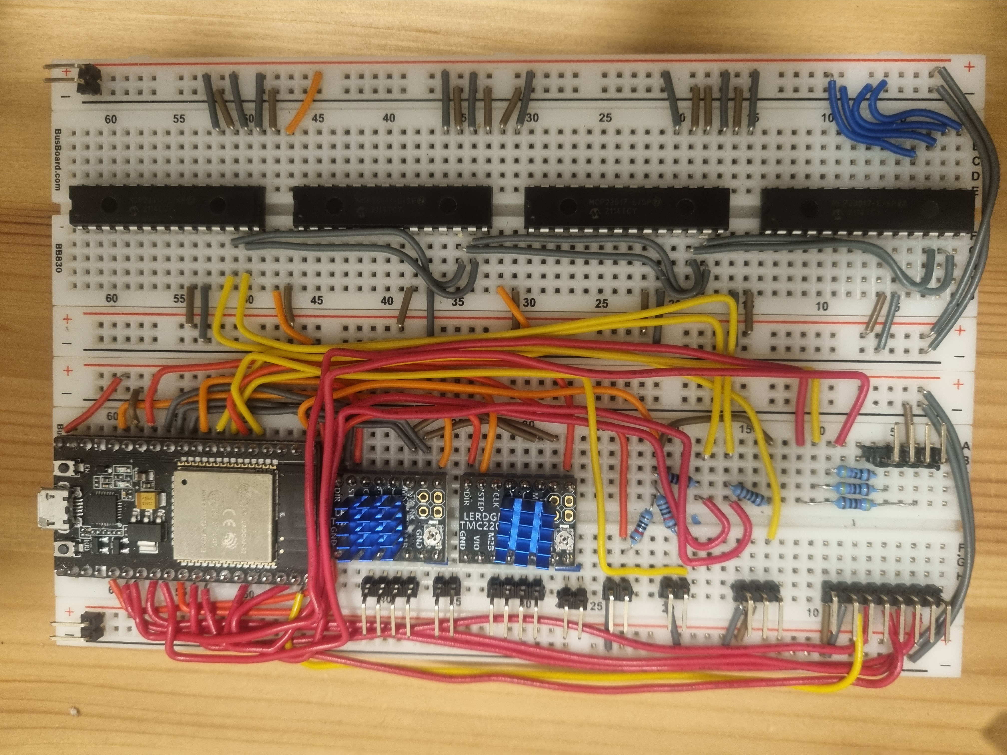
Imgaes/WIP/20220914_021122.jpg
