Yakir-Shlez/AutoChess/Imgaes/WIP/20220914_030019.jpg

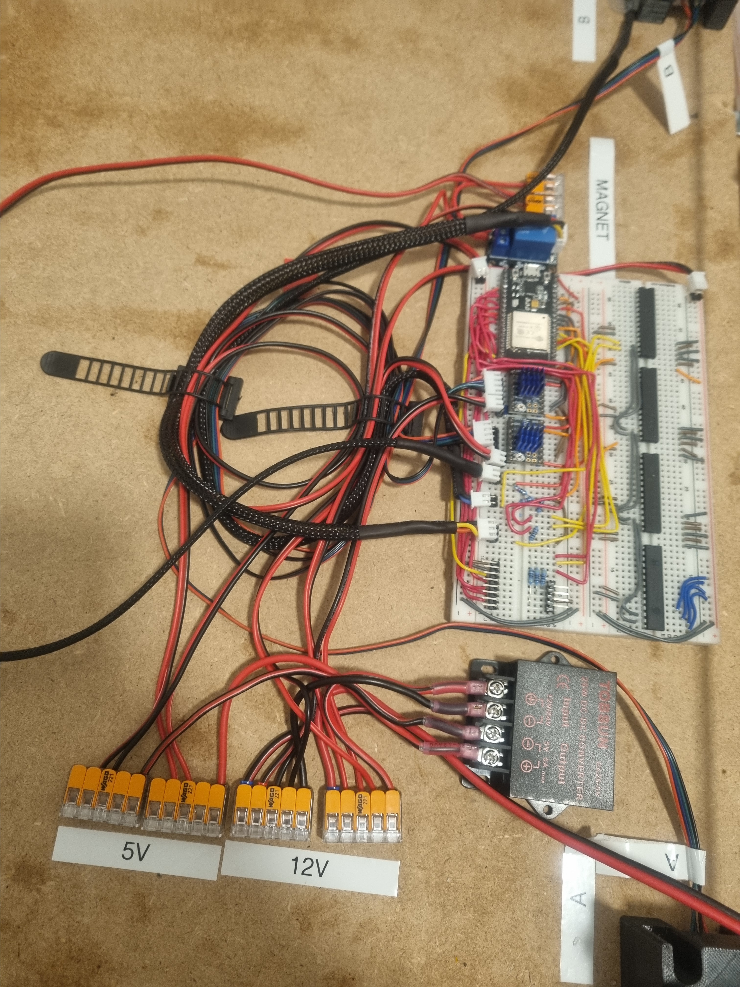
Imgaes/WIP/20220914_030019.jpg
