Yakir-Shlez/AutoChess/Imgaes/WIP/20220914_030029.jpg

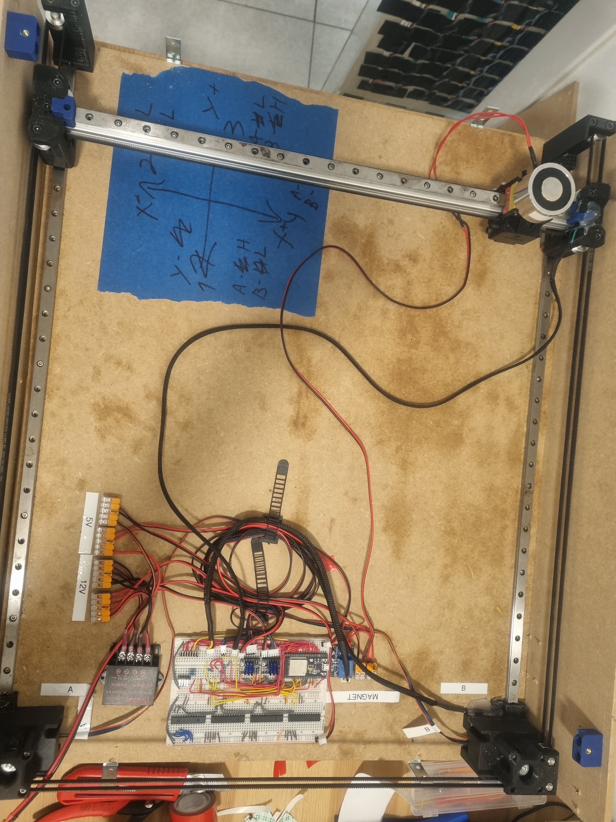
Imgaes/WIP/20220914_030029.jpg
