Yakir-Shlez/AutoChess/Imgaes/WIP/20220917_202512.jpg

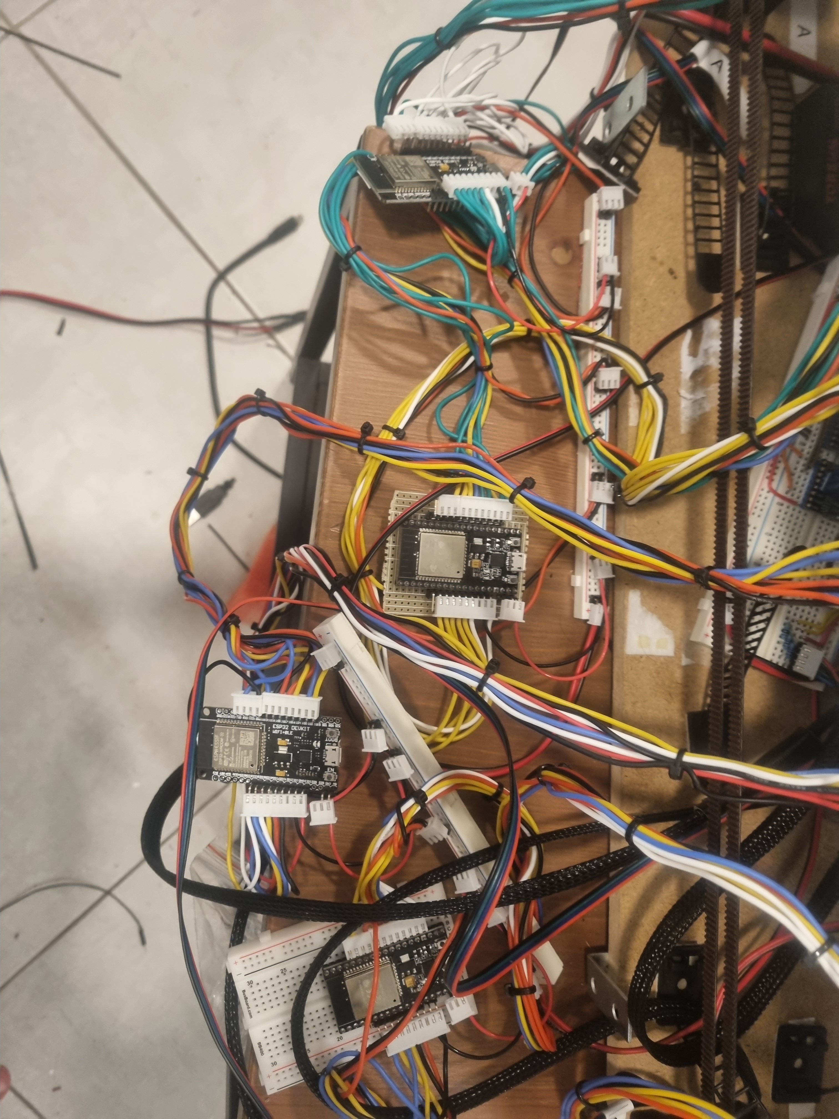
Imgaes/WIP/20220917_202512.jpg
