Yakir-Shlez/AutoChess/Imgaes/WIP/20220917_202611.jpg

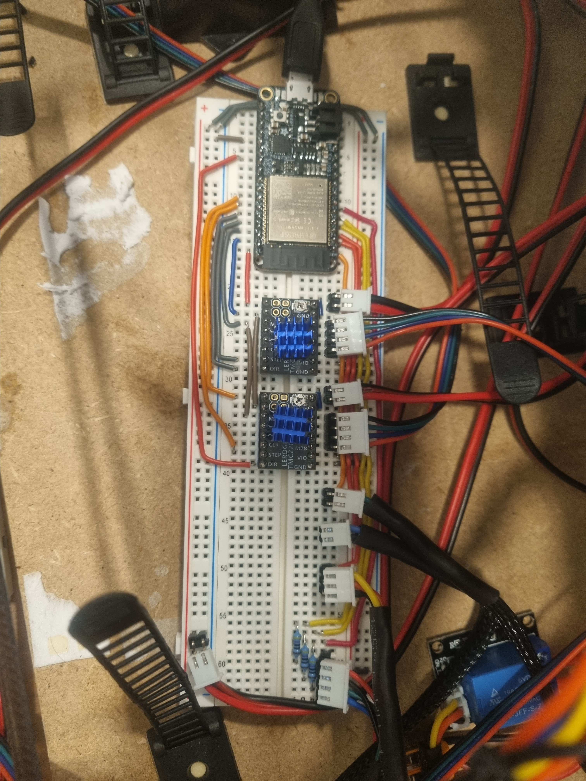
Imgaes/WIP/20220917_202611.jpg
